andimoto/keebcu/pics/75er008.png

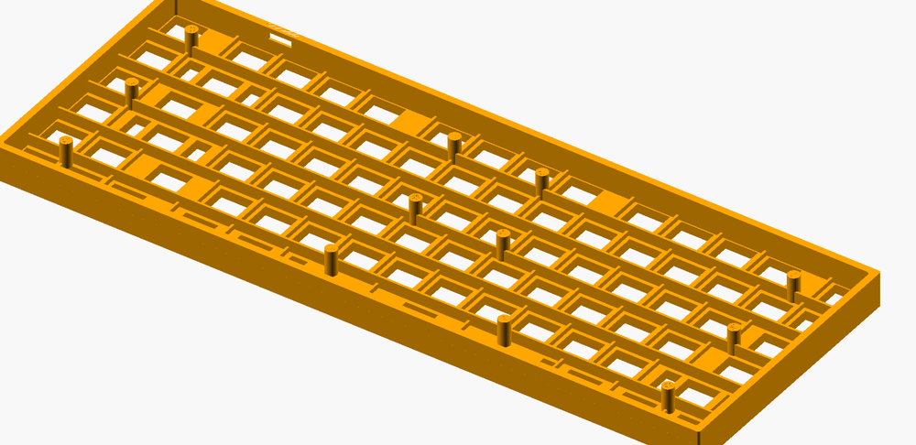
pics/75er008.png
