andimoto/keebcu/pics/75er014.png

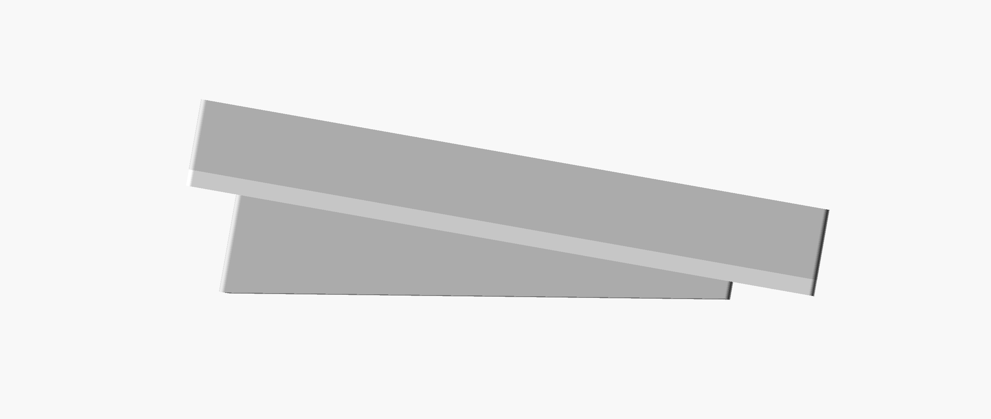
pics/75er014.png
