andimoto/keebcu/pics/75er015.png

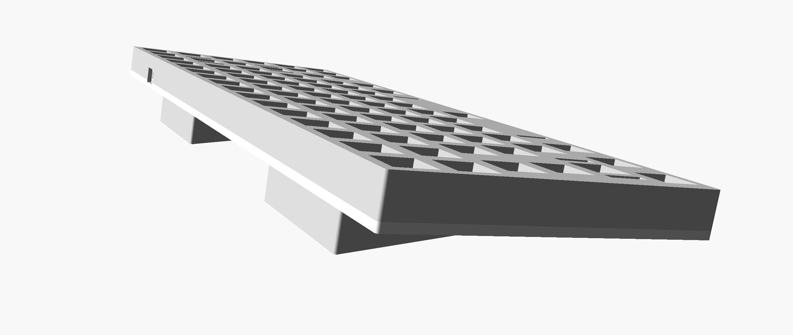
pics/75er015.png
