andimoto/keebcu/pics/75er016.png

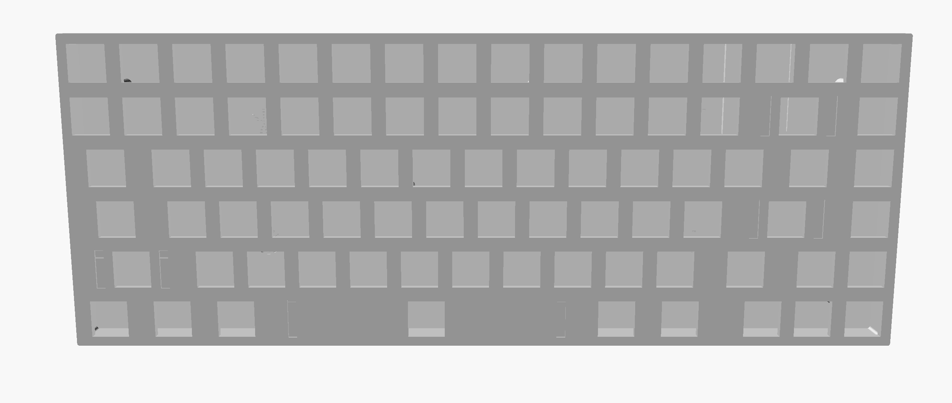
pics/75er016.png
