andimoto/keebcu/pics/75er017.png

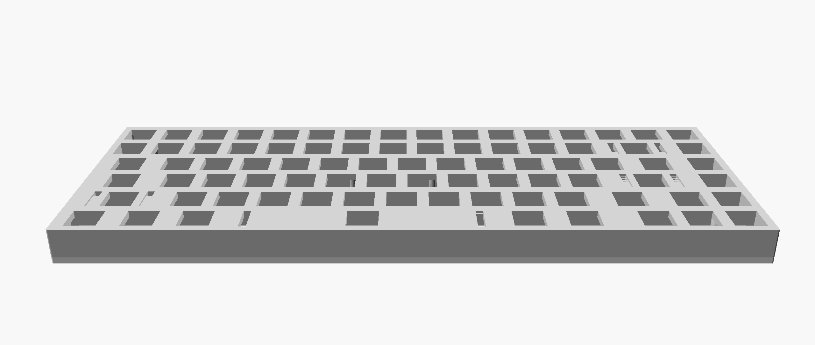
pics/75er017.png
