andimoto/keebcu/pics/andimoto7583-xda001.png

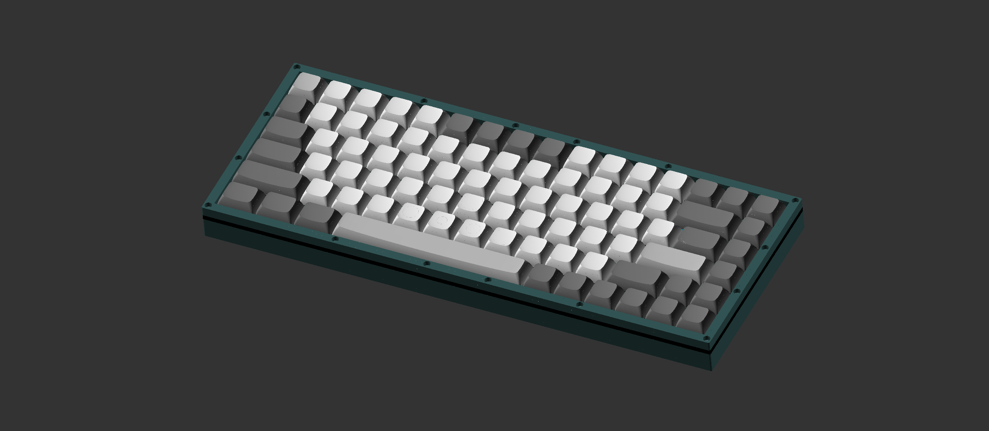
pics/andimoto7583-xda001.png
