andimoto/keebcu/pics/andimoto7583-xda002.png

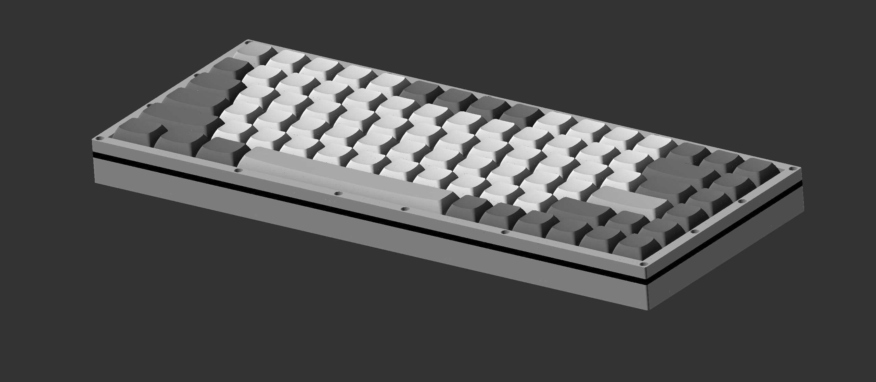
pics/andimoto7583-xda002.png
