andimoto/keebcu/pics/costar_stabs.png

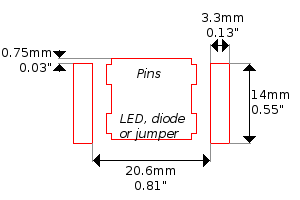
pics/costar_stabs.png
