andimoto/keebcu/pics/img/IMG_20201101_000850.jpg

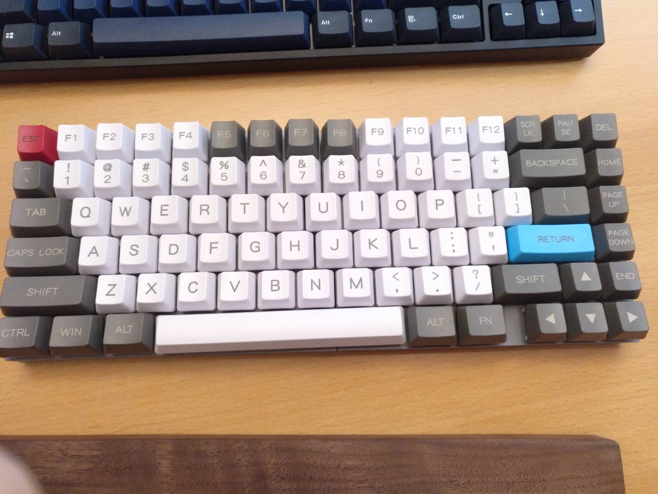
pics/img/IMG_20201101_000850.jpg
