andimoto/keebcu/pics/img/IMG_20201101_000857.jpg

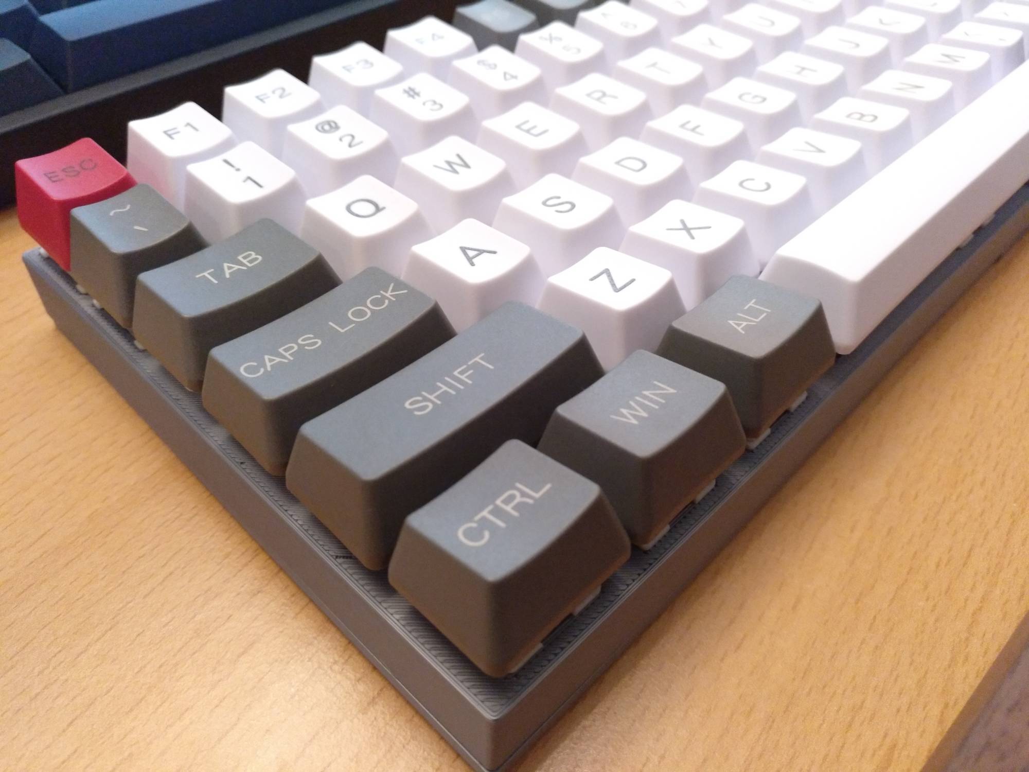
pics/img/IMG_20201101_000857.jpg
