andimoto/keebcu/pics/img/IMG_20201101_000921.jpg

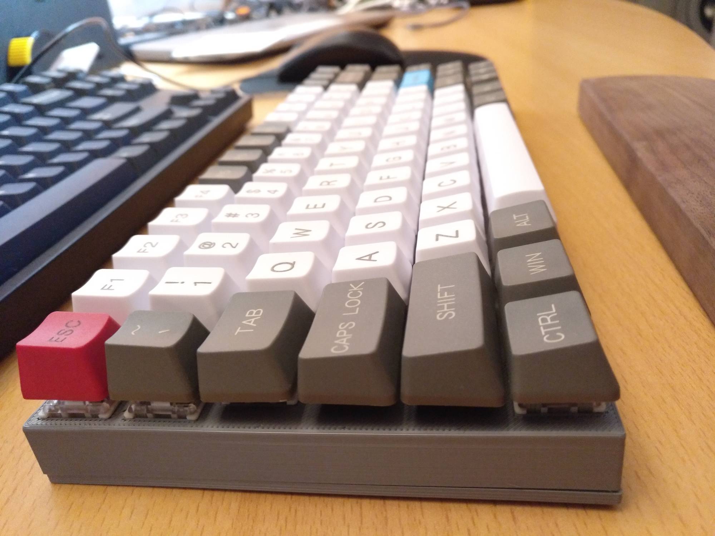
pics/img/IMG_20201101_000921.jpg
