andimoto/keebcu/pics/img/IMG_20201101_000947.jpg

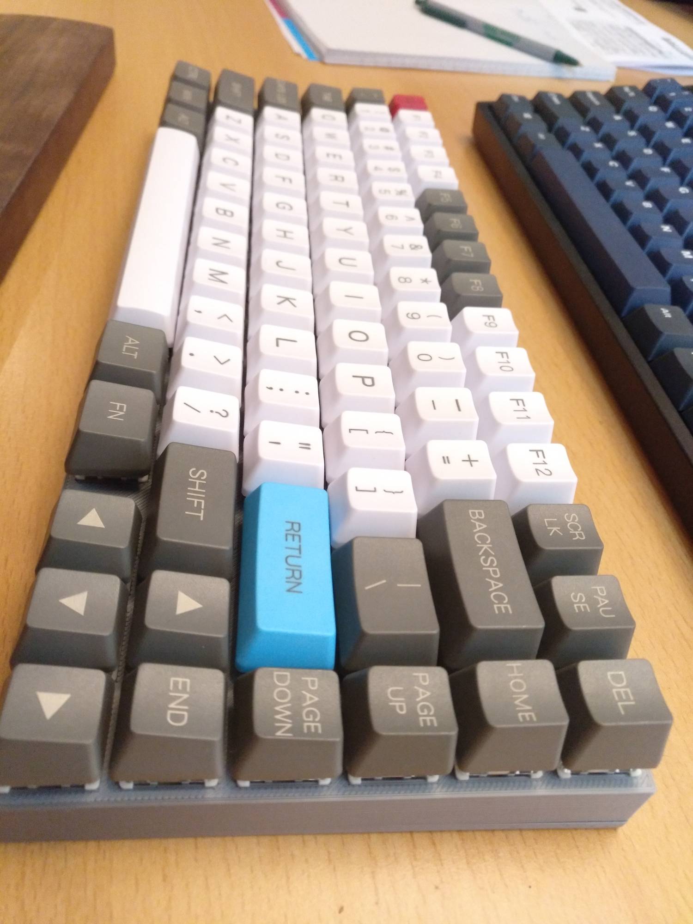
pics/img/IMG_20201101_000947.jpg
