andimoto/keebcu/pics/img/IMG_20201101_001009.jpg

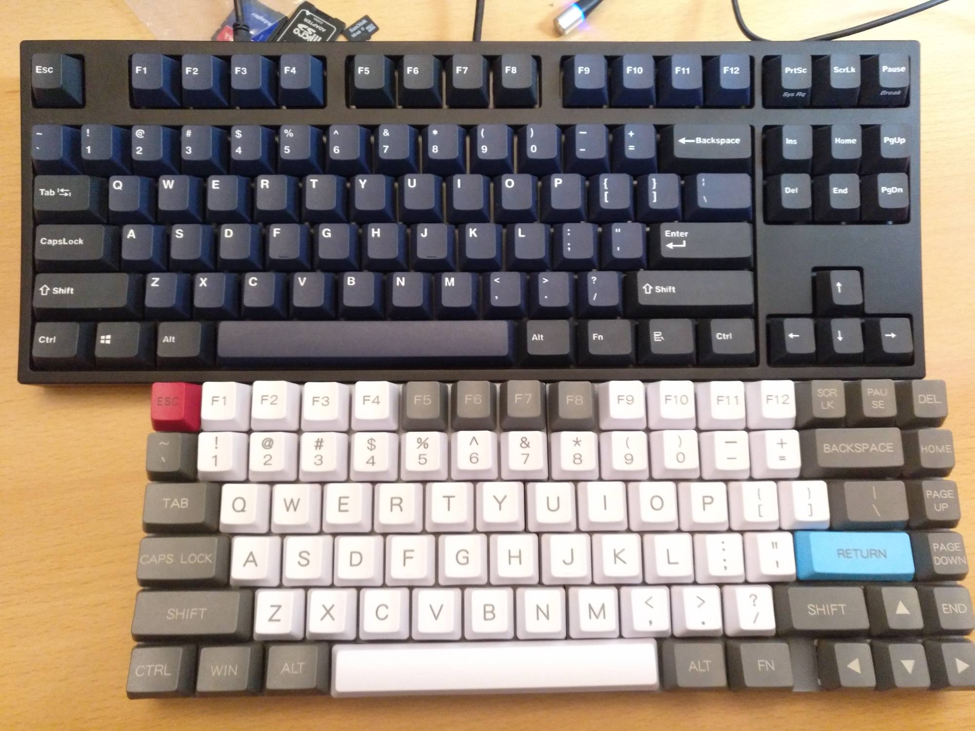
pics/img/IMG_20201101_001009.jpg
