andimoto/keebcu/pics/img/IMG_20201101_001109.jpg

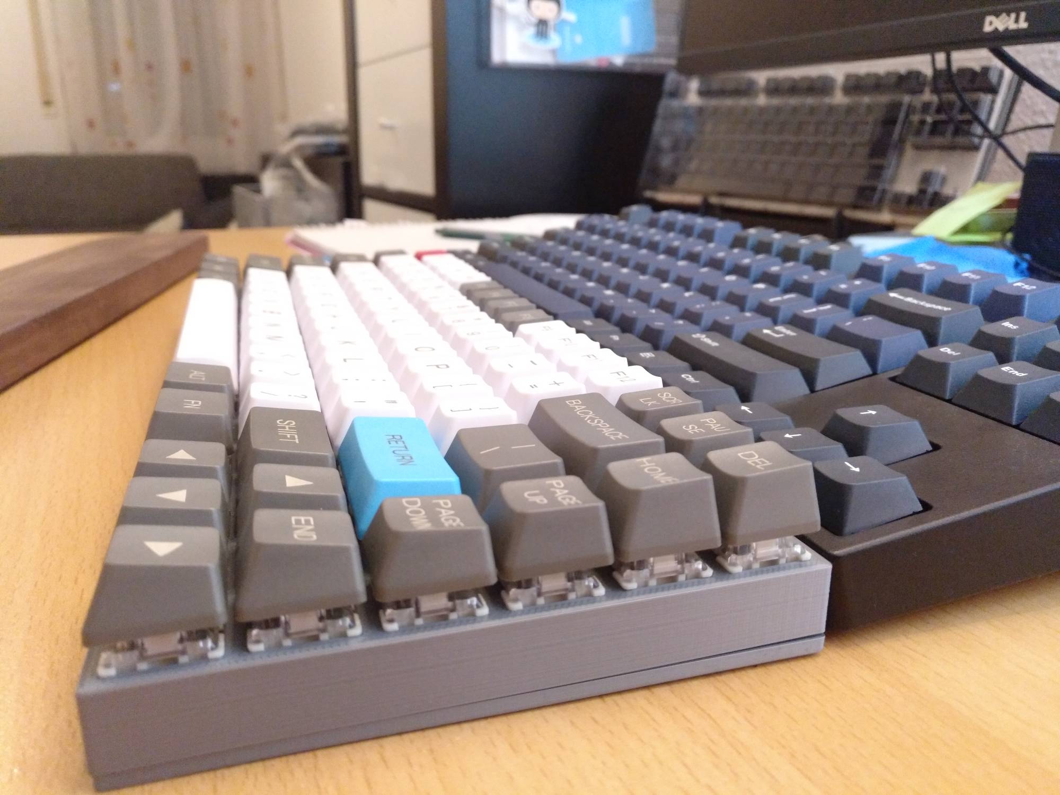
pics/img/IMG_20201101_001109.jpg
