andimoto/keebcu/pics/img/IMG_20201224_110359.jpg

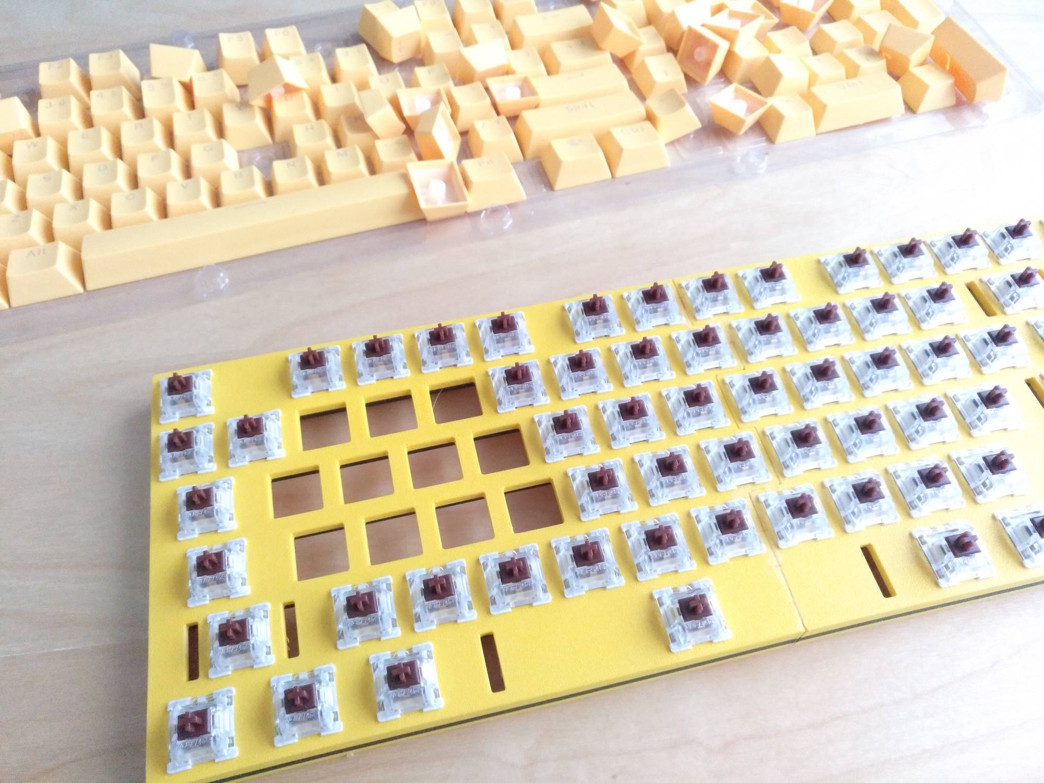
pics/img/IMG_20201224_110359.jpg
