andimoto/keebcu/pics/img/IMG_20201224_111618.jpg

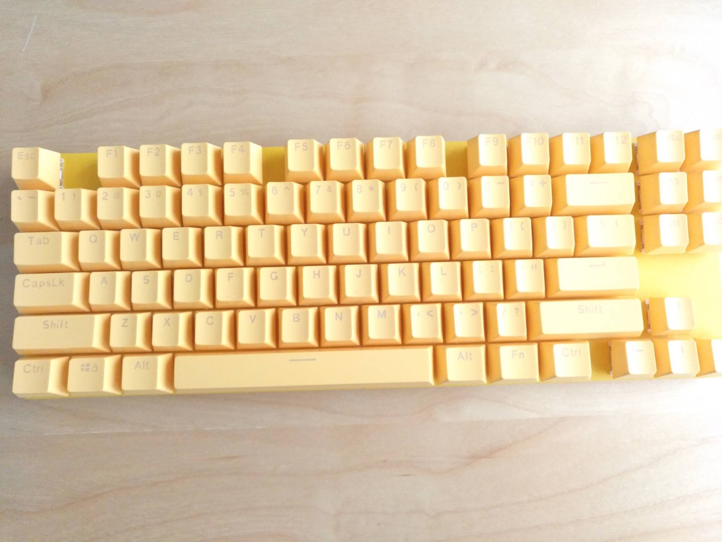
pics/img/IMG_20201224_111618.jpg
