andimoto/keebcu/pics/img/IMG_20201224_111624.jpg

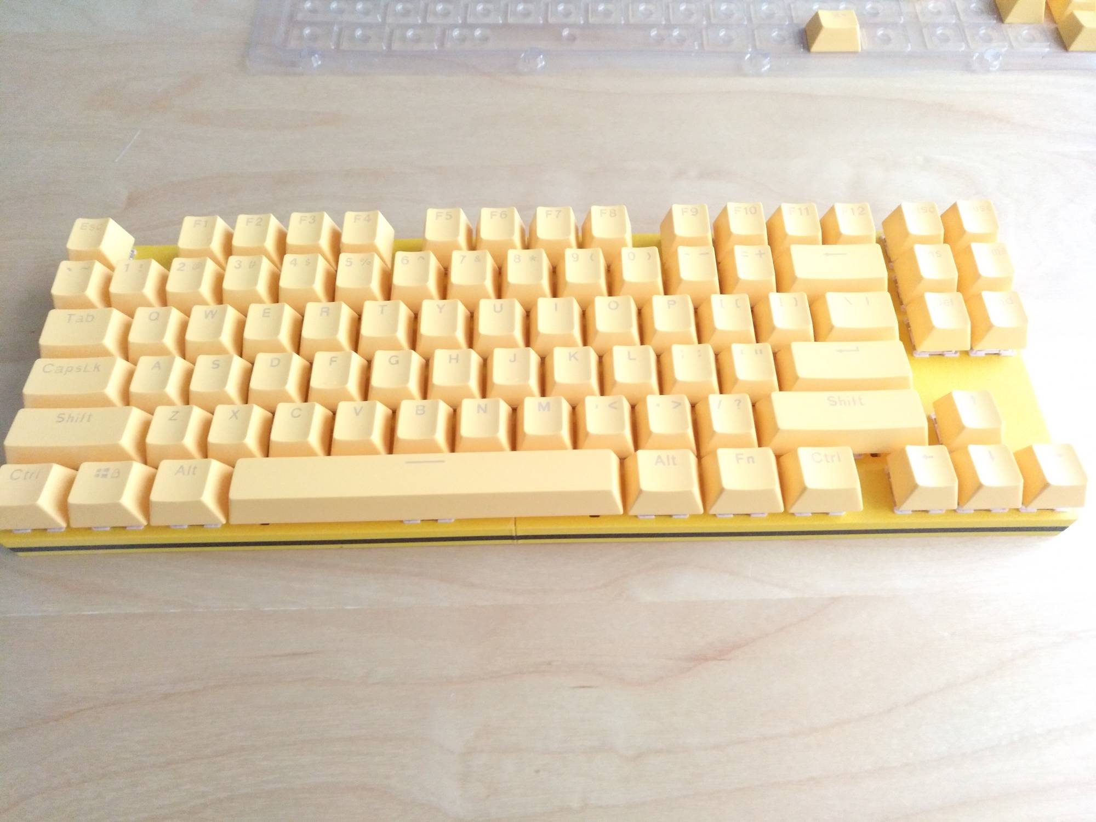
pics/img/IMG_20201224_111624.jpg
