andimoto/keebcu/pics/img/IMG_20201224_111630.jpg

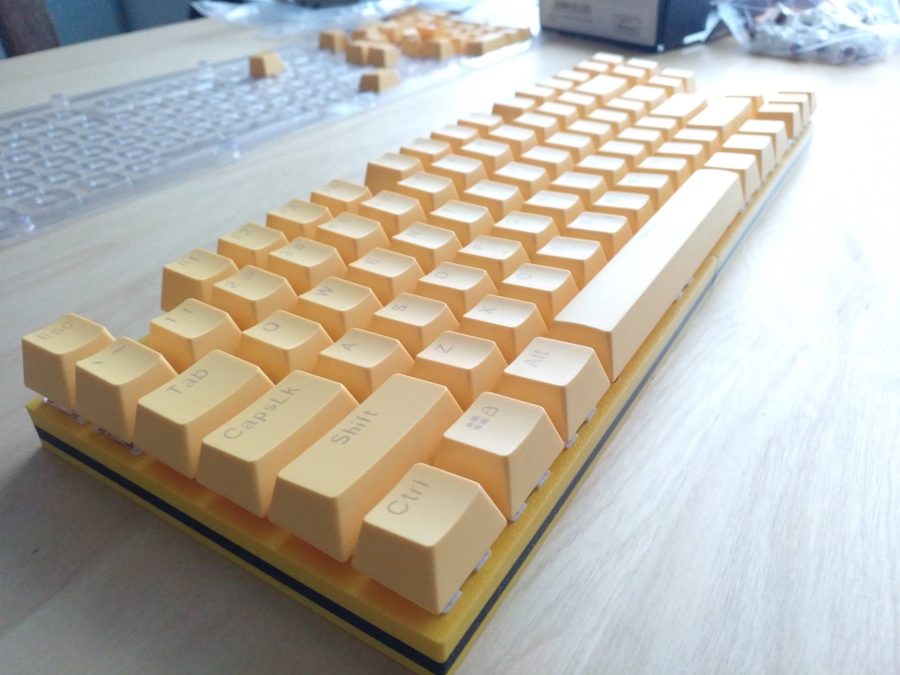
pics/img/IMG_20201224_111630.jpg
