andimoto/keebcu/pics/img/IMG_20201224_111640.jpg

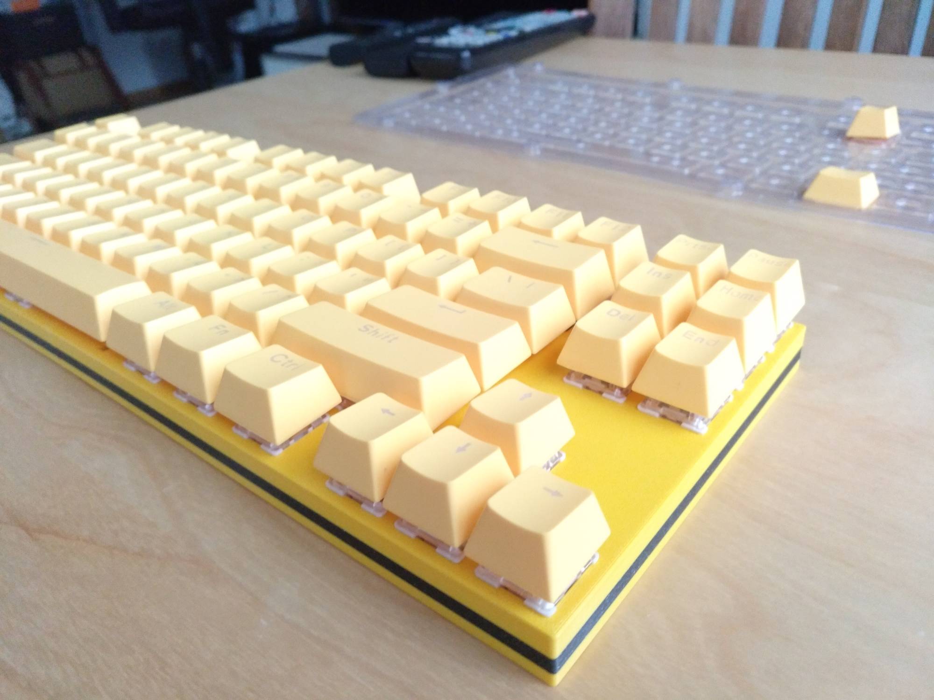
pics/img/IMG_20201224_111640.jpg
