andimoto/keebcu/pics/img/IMG_20201224_111739.jpg

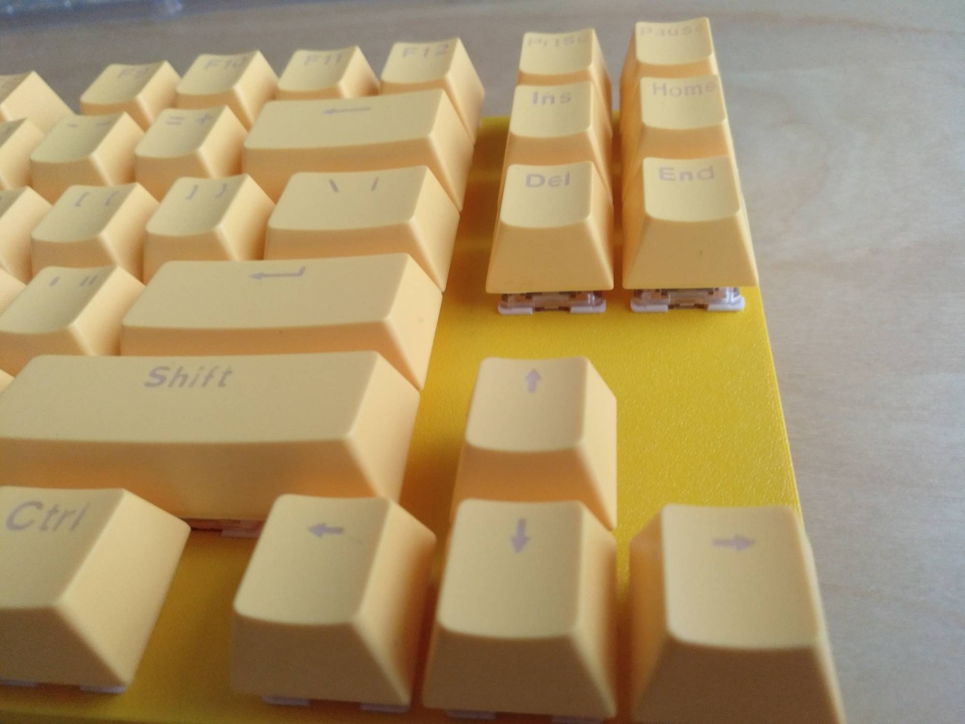
pics/img/IMG_20201224_111739.jpg
