andimoto/keebcu/pics/img/IMG_20201224_111744.jpg

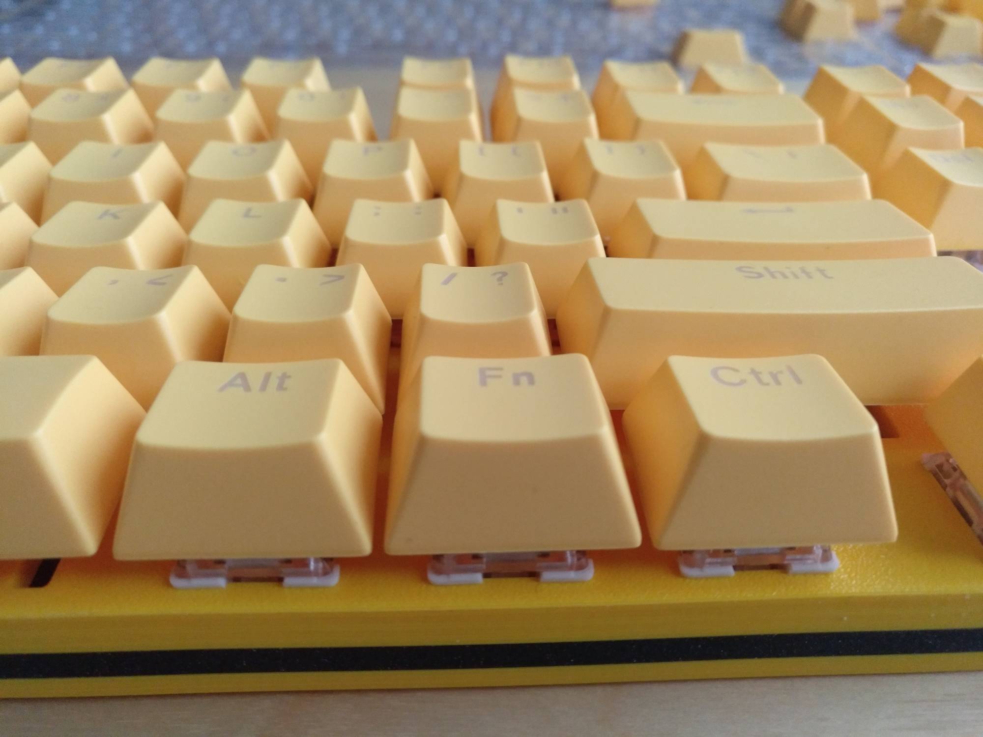
pics/img/IMG_20201224_111744.jpg
