andimoto/keebcu/pics/img/IMG_20201224_111752.jpg

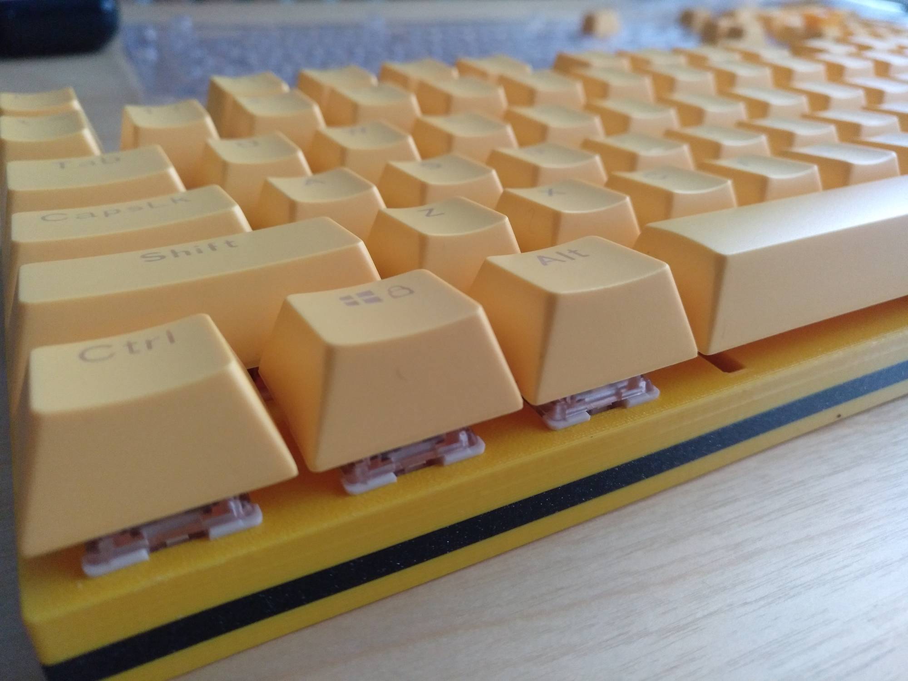
pics/img/IMG_20201224_111752.jpg
