andimoto/keebcu/pics/img/IMG_20201228_204647.jpg

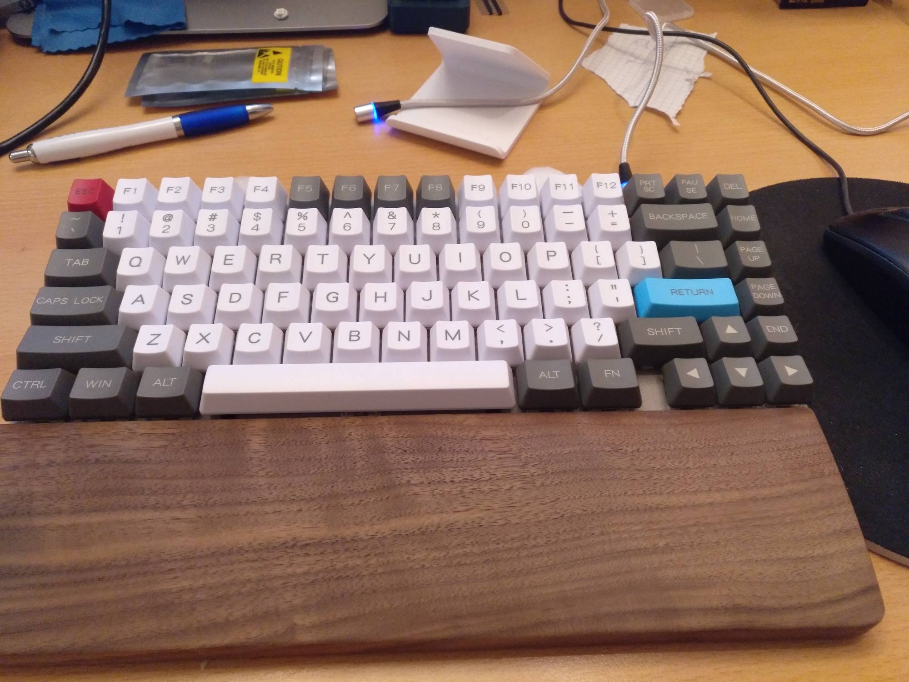
pics/img/IMG_20201228_204647.jpg
