andimoto/keebcu/pics/img/IMG_20210111_151033.jpg

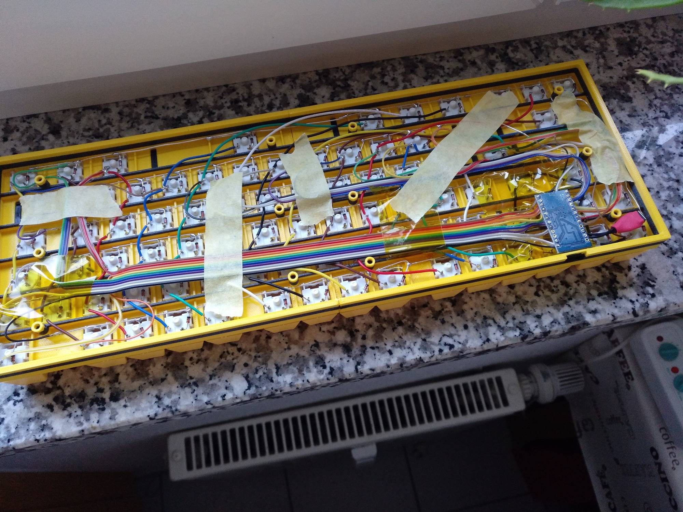
pics/img/IMG_20210111_151033.jpg
