andimoto/keebcu/pics/img/IMG_20210111_151047.jpg

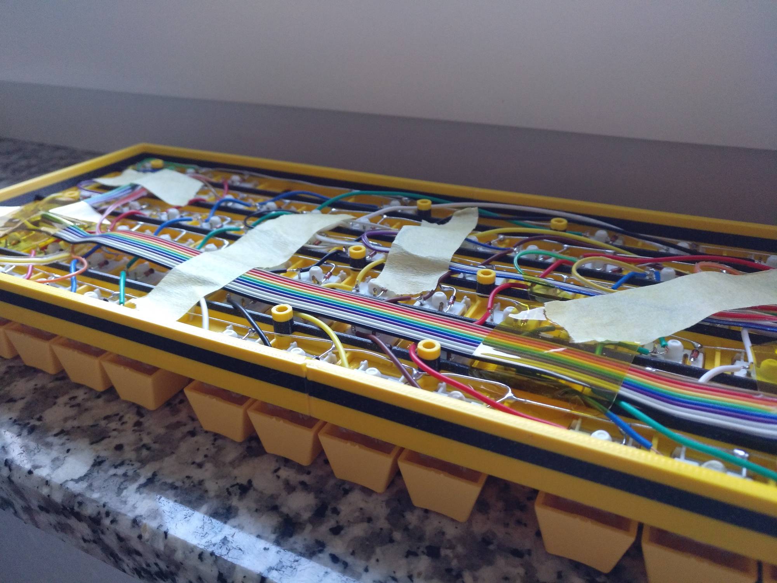
pics/img/IMG_20210111_151047.jpg
