andimoto/keebcu/pics/img/IMG_20210111_151052.jpg

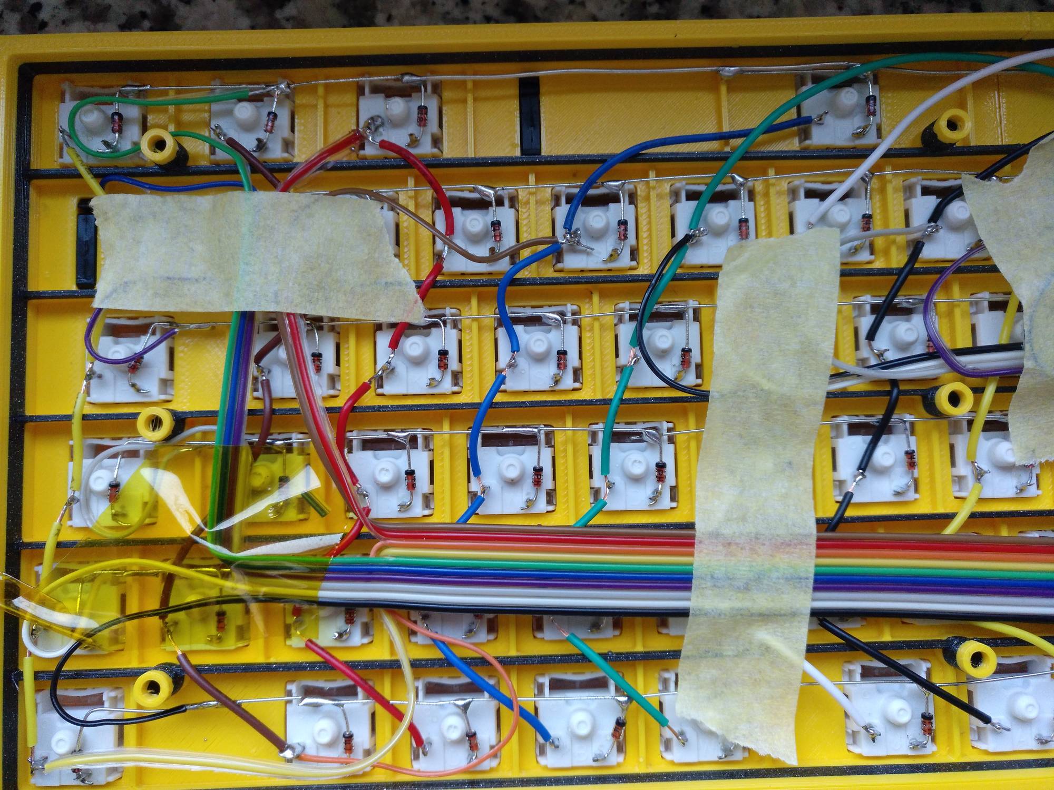
pics/img/IMG_20210111_151052.jpg
