andimoto/keebcu/pics/img/IMG_20210111_151100.jpg

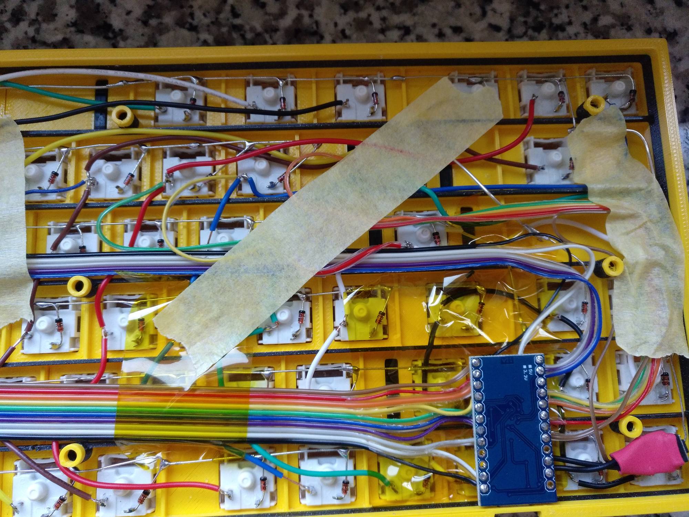
pics/img/IMG_20210111_151100.jpg
