andimoto/keebcu/pics/img/IMG_20210111_151114.jpg

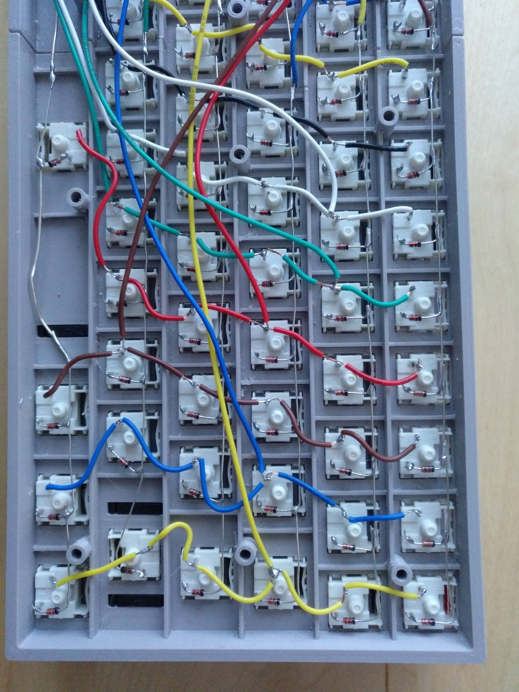
pics/img/IMG_20210111_151114.jpg
