andimoto/keebcu/pics/img/IMG_20210111_151118.jpg

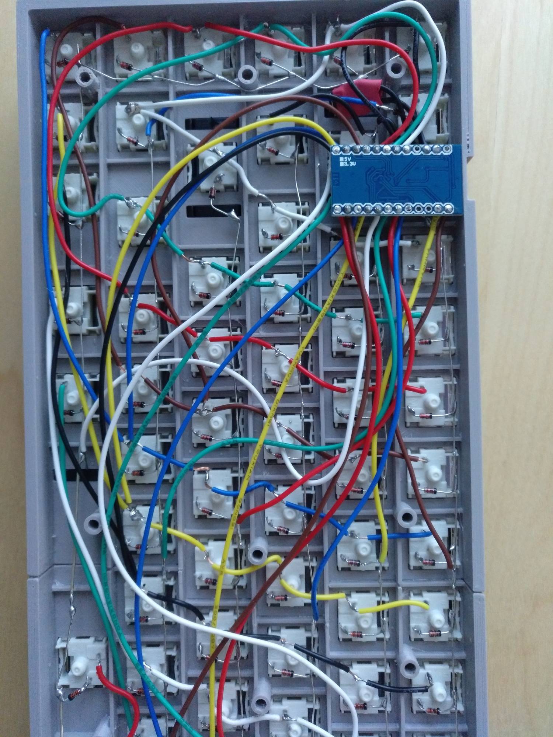
pics/img/IMG_20210111_151118.jpg
