andimoto/keebcu/pics/img/IMG_20210119_213742.jpg

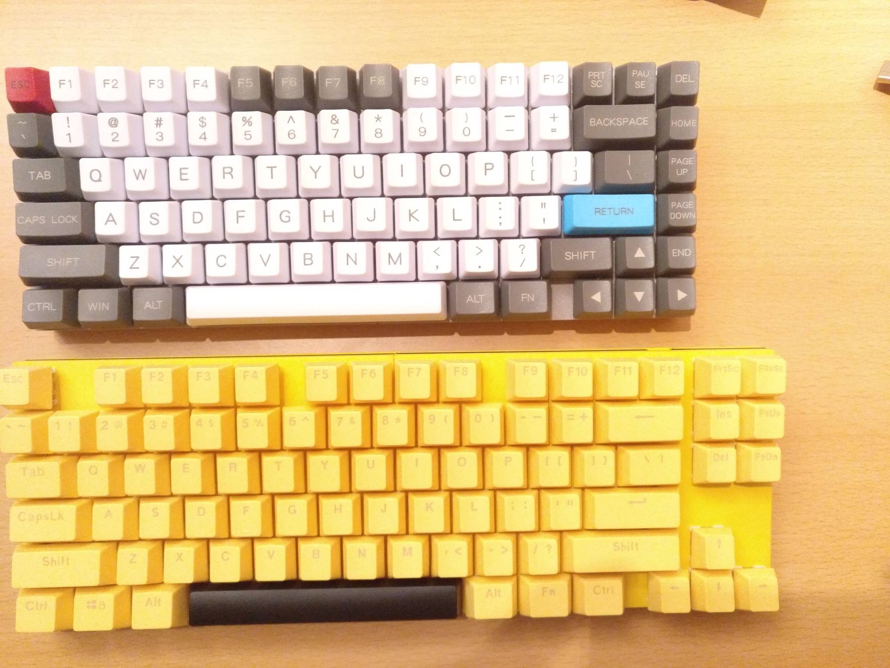
pics/img/IMG_20210119_213742.jpg
