andimoto/keebcu/pics/img/IMG_20210318_140613.jpg

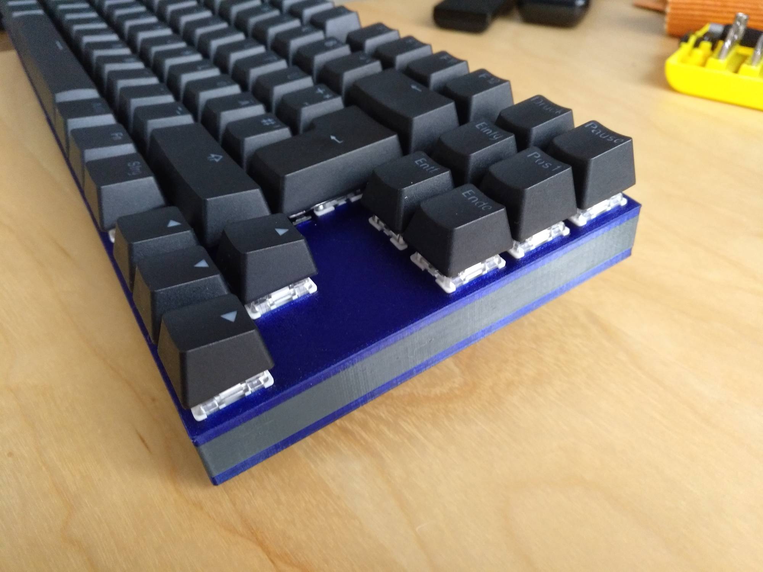
pics/img/IMG_20210318_140613.jpg
