andimoto/keebcu/pics/img/IMG_20210318_140618.jpg

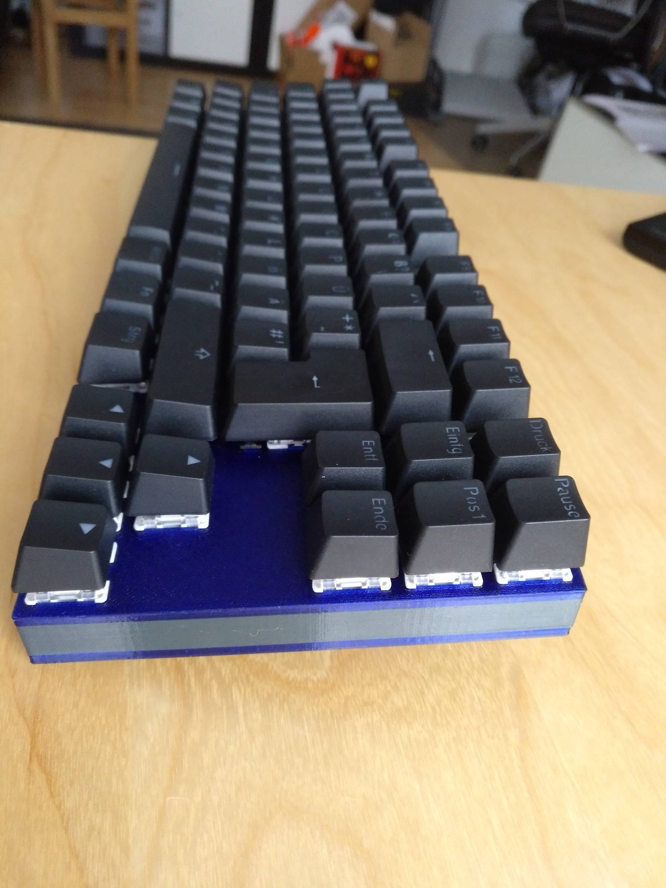
pics/img/IMG_20210318_140618.jpg
