andimoto/keebcu/pics/img/IMG_20210318_140654.jpg

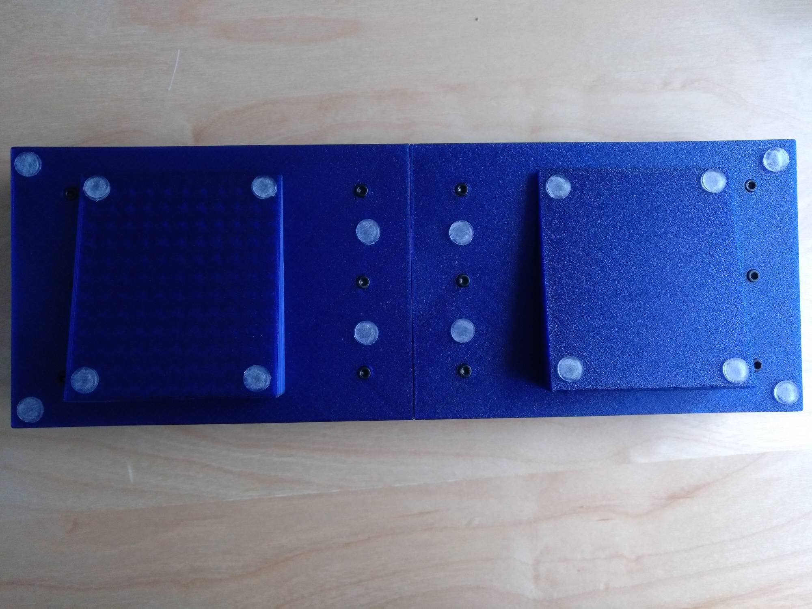
pics/img/IMG_20210318_140654.jpg
