andimoto/keebcu/pics/img/IMG_20210318_175820.jpg

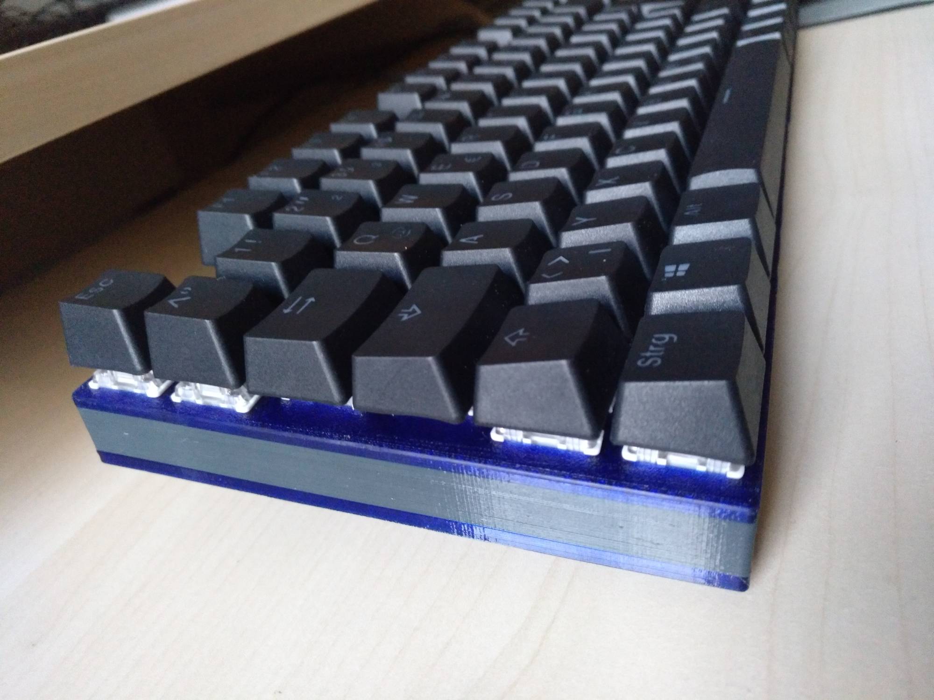
pics/img/IMG_20210318_175820.jpg
