andimoto/keebcu/pics/img/IMG_20210318_175835.jpg

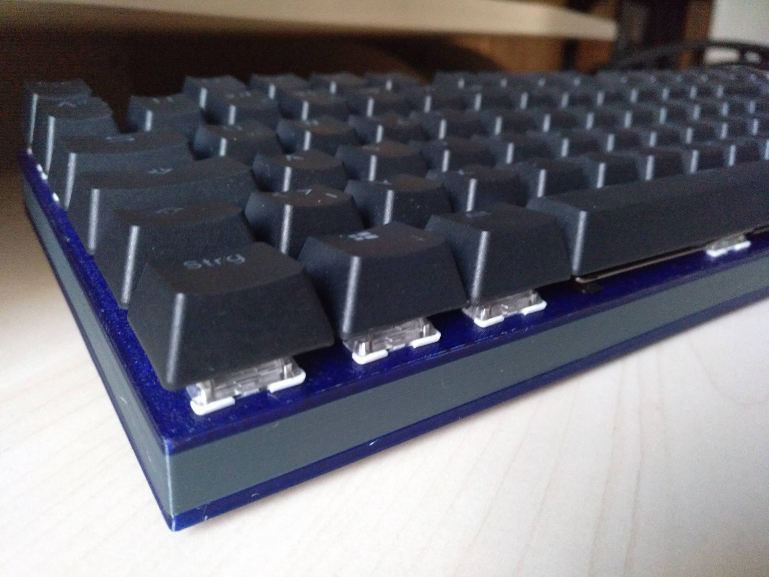
pics/img/IMG_20210318_175835.jpg
