andimoto/keebcu/pics/img/IMG_20210405_204525.jpg

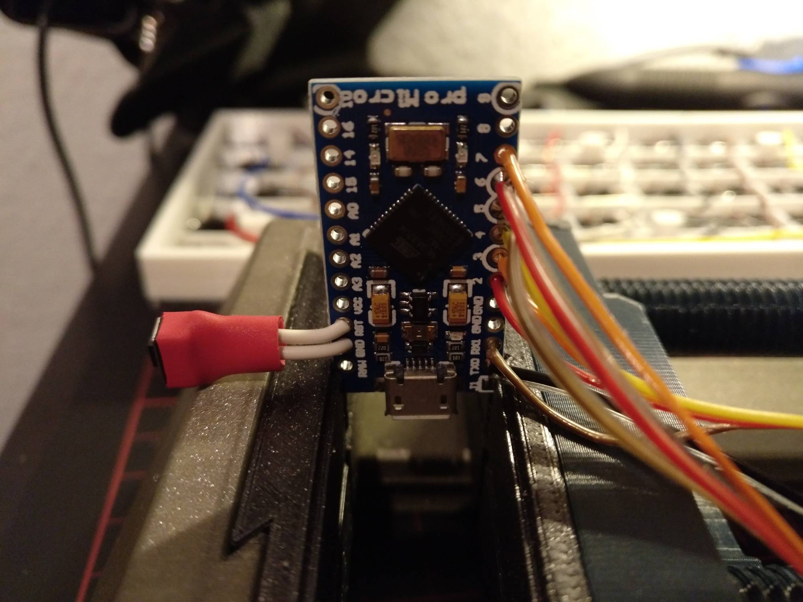
pics/img/IMG_20210405_204525.jpg
