andimoto/keebcu/pics/img/IMG_20210406_151226.jpg

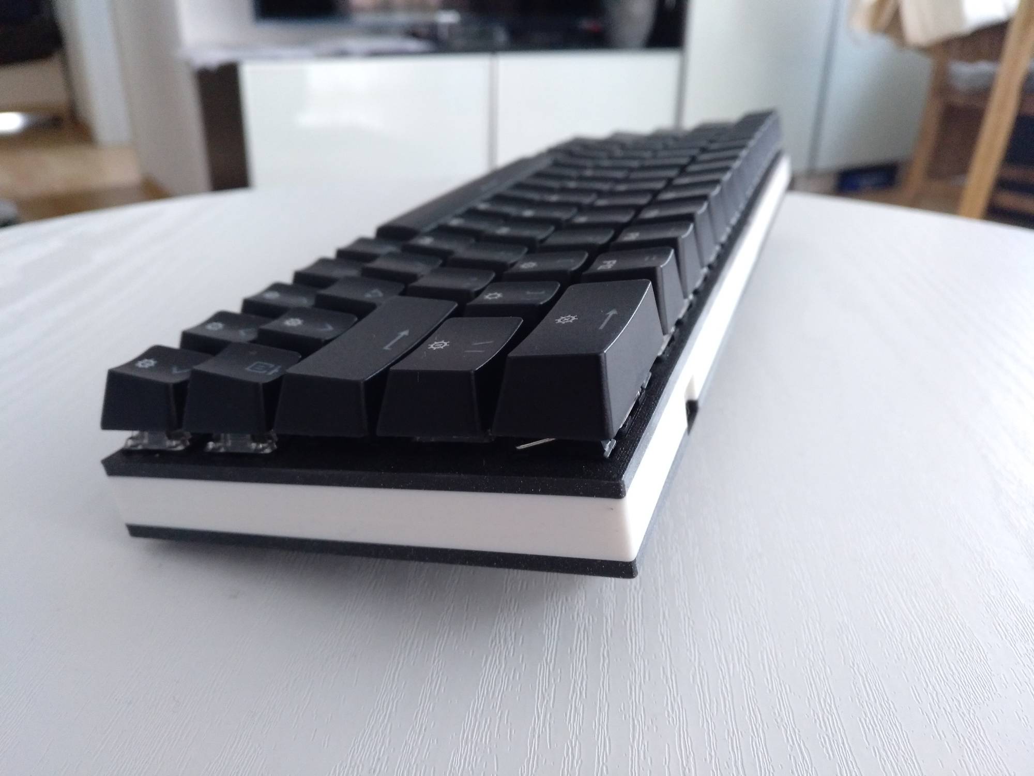
pics/img/IMG_20210406_151226.jpg
