andimoto/keebcu/pics/img/IMG_20210406_151432.jpg

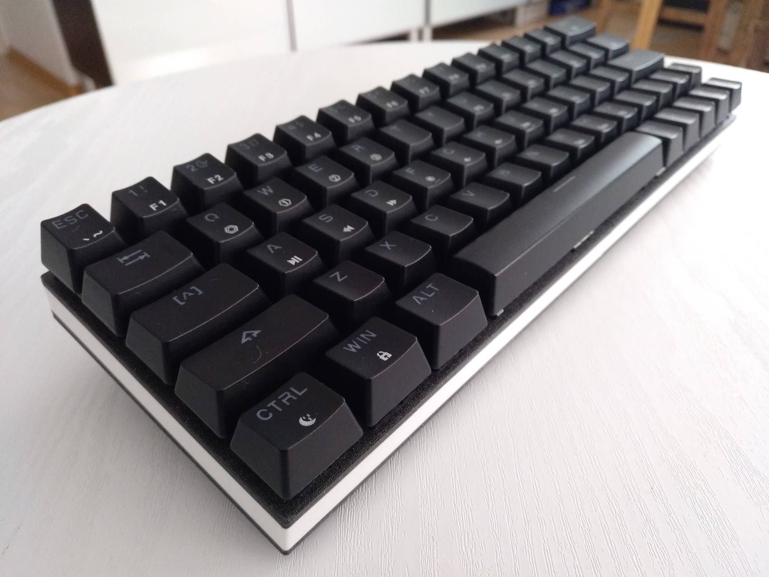
pics/img/IMG_20210406_151432.jpg
