andimoto/keebcu/pics/img/IMG_20210406_151457.jpg

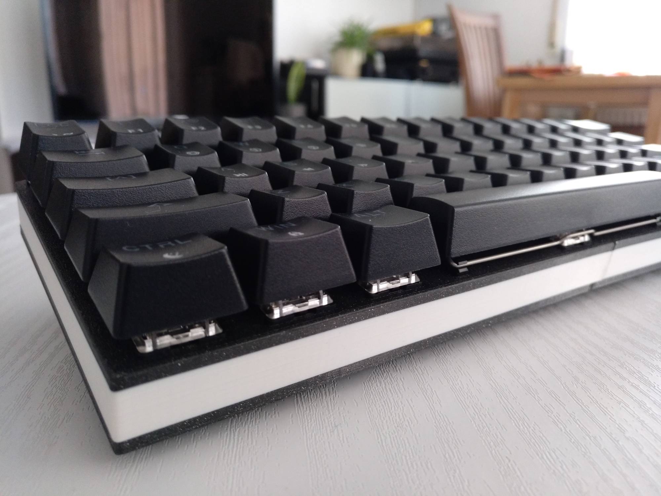
pics/img/IMG_20210406_151457.jpg
