andimoto/keebcu/pics/img/screwHolesColorChange.jpg

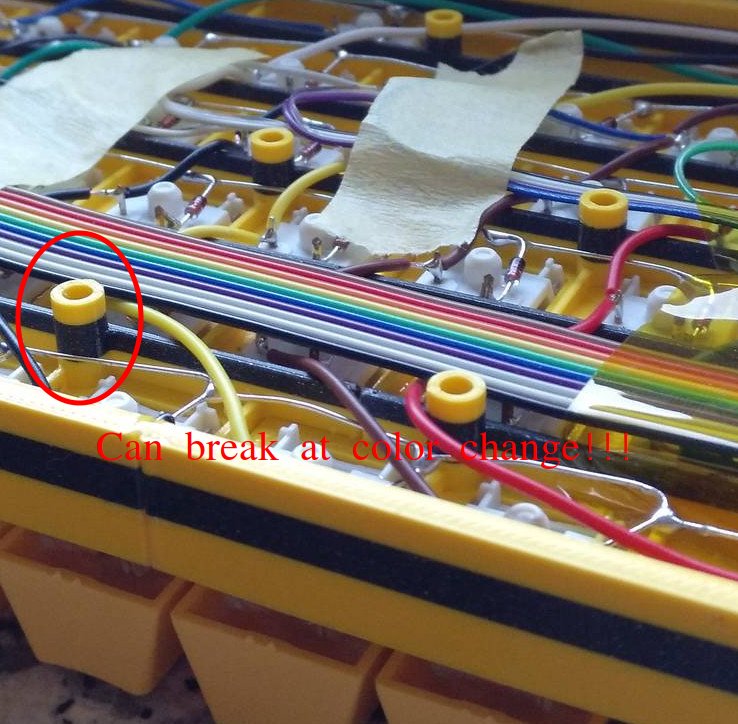
pics/img/screwHolesColorChange.jpg
