andimoto/keebcu/pics/pics/andimoto75Q1iso-001.jpg

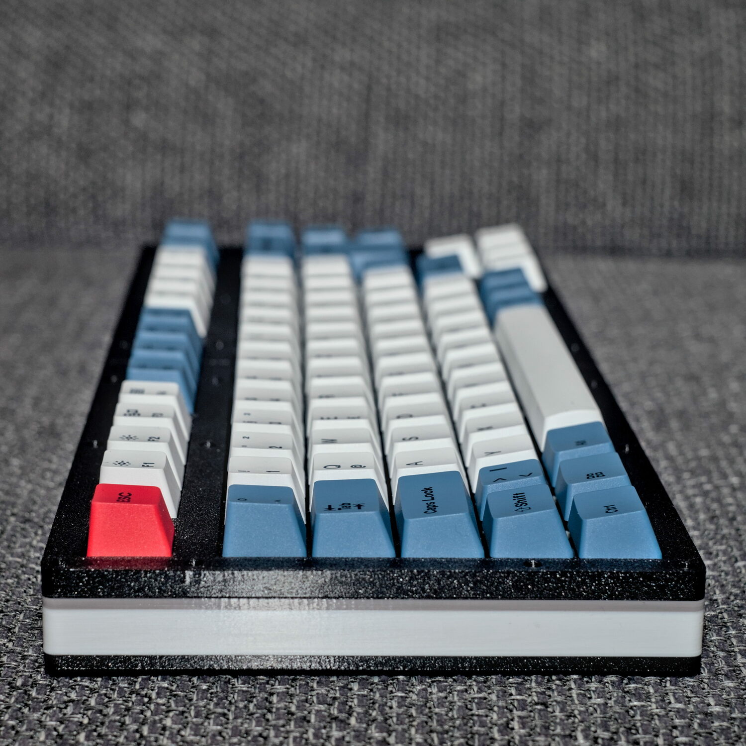
pics/pics/andimoto75Q1iso-001.jpg
