andimoto/keebcu/pics/pics/andimoto75Q1iso-003.jpg

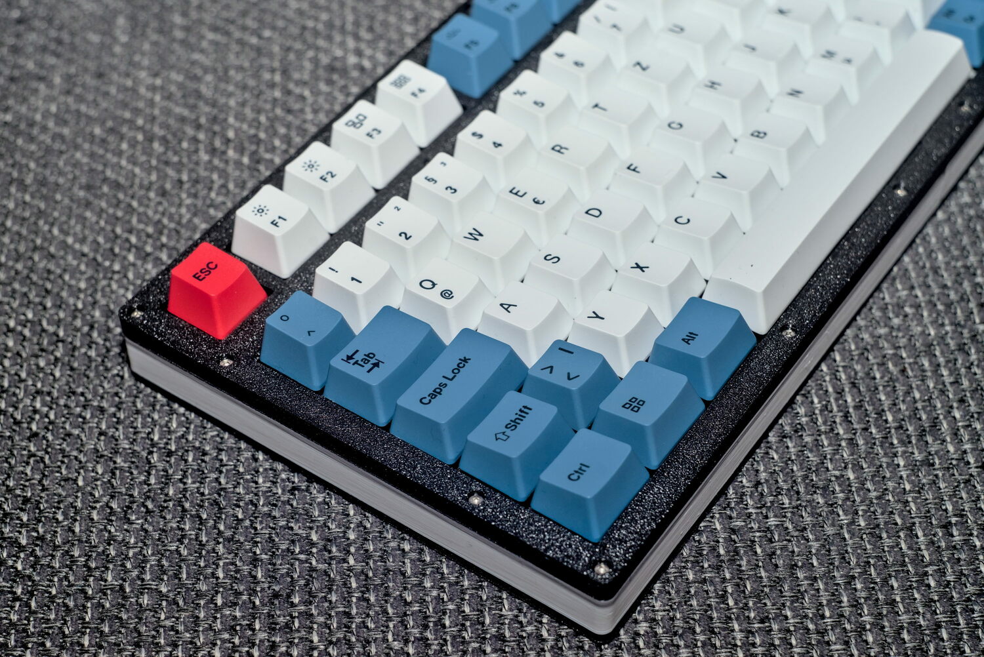
pics/pics/andimoto75Q1iso-003.jpg
