andimoto/keebcu/pics/pics/andimoto75Q1iso-005.jpg

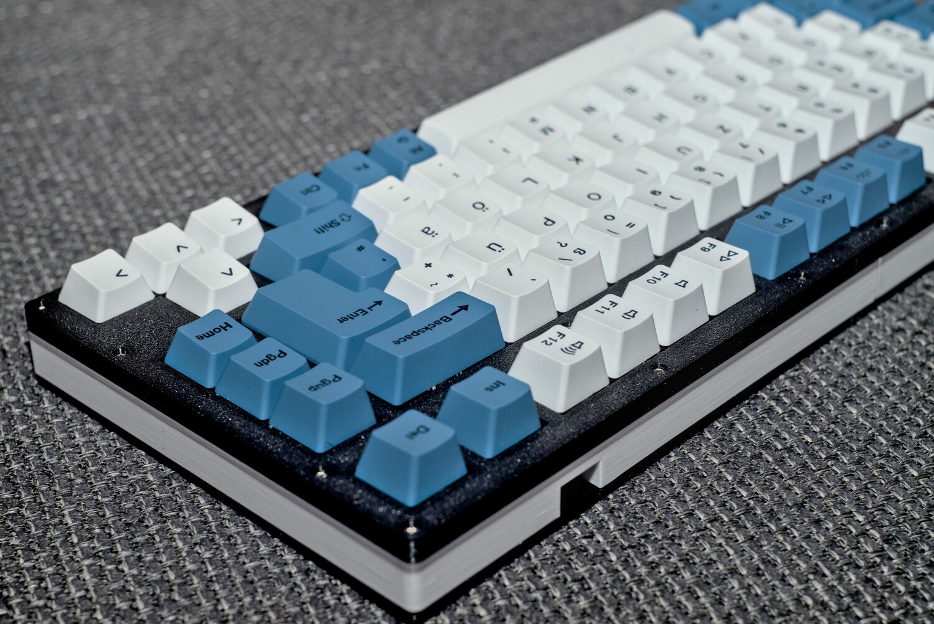
pics/pics/andimoto75Q1iso-005.jpg
