andimoto/keebcu/pics/pics/andimoto75Q1iso-008.jpg

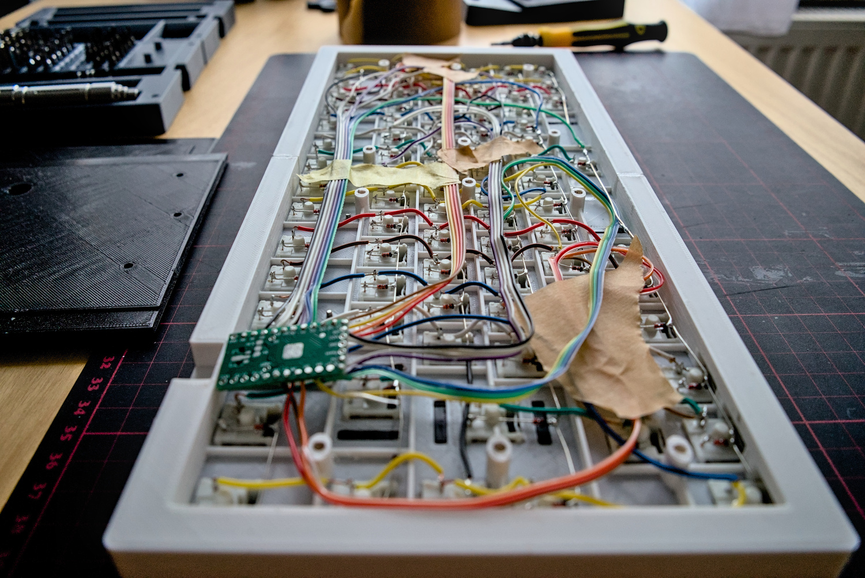
pics/pics/andimoto75Q1iso-008.jpg
