andimoto/keebcu/pics/pics/andimoto75Q1iso-009.jpg

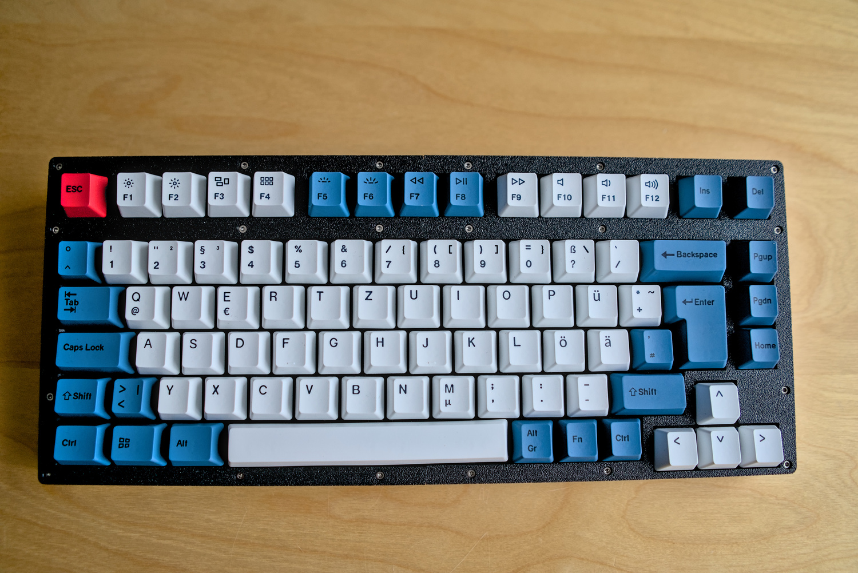
pics/pics/andimoto75Q1iso-009.jpg
