andimoto/keebcu/pics/pics/andimoto75Q1iso-010.jpg

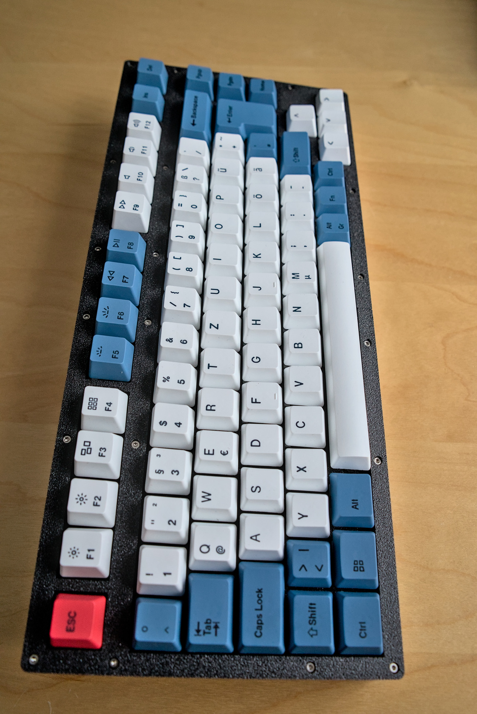
pics/pics/andimoto75Q1iso-010.jpg
