andimoto/keebcu/pics/pics/andimoto75Q1iso-011.jpg

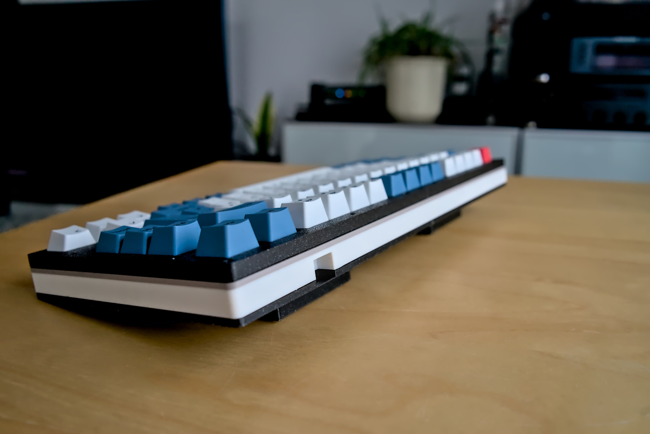
pics/pics/andimoto75Q1iso-011.jpg
