andimoto/keebcu/pics/pics/andimoto75Q1iso-012.jpg

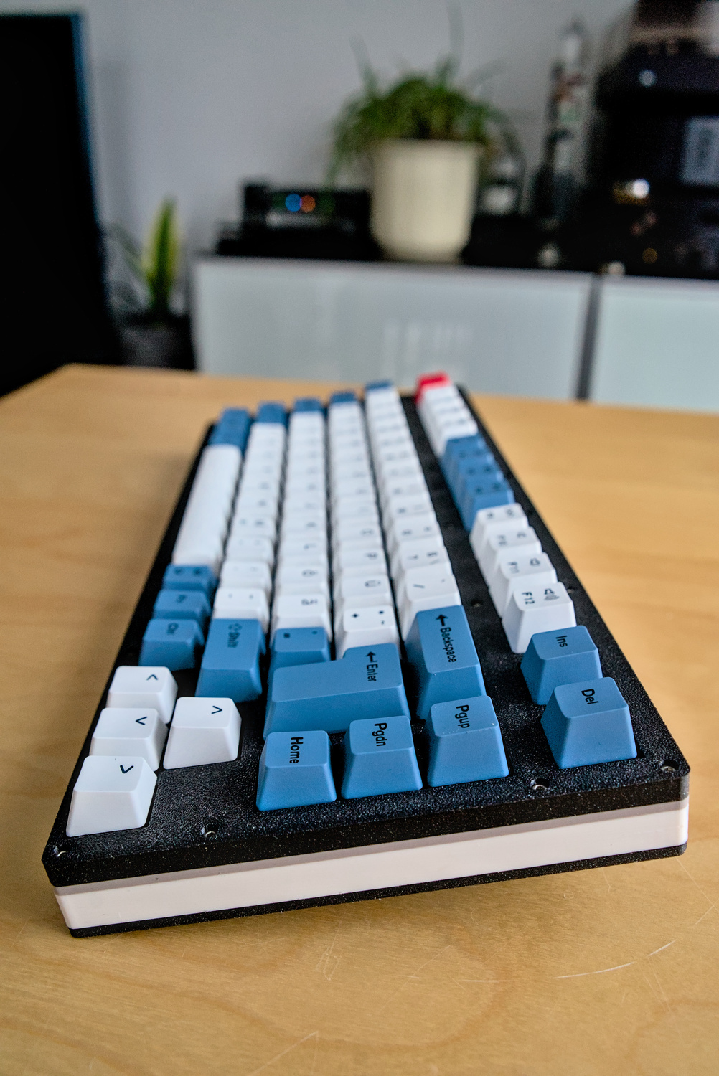
pics/pics/andimoto75Q1iso-012.jpg
