andimoto/keebcu/pics/pics/keebcu_002.JPG

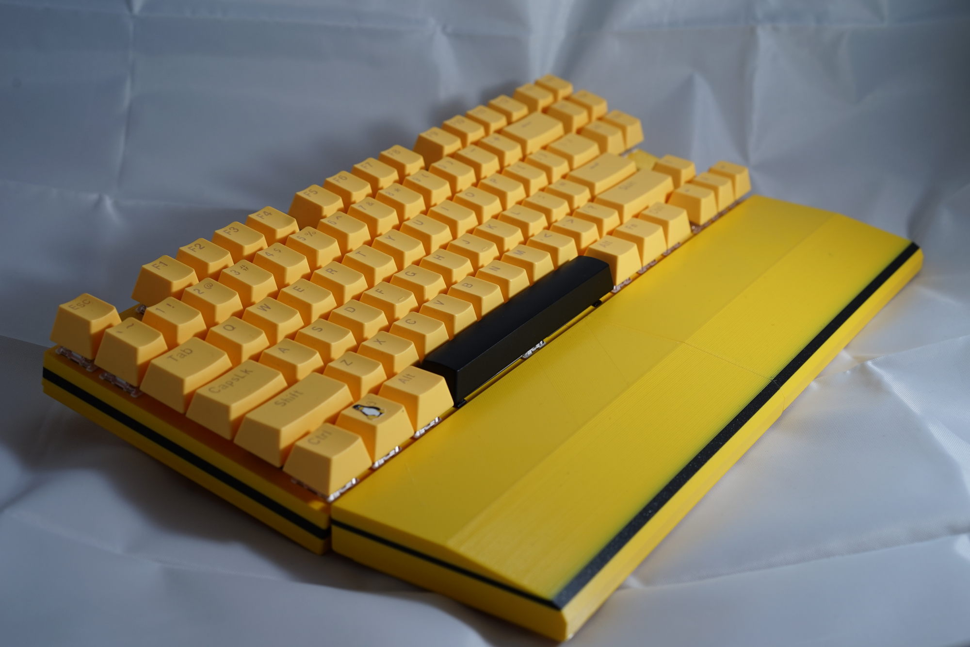
pics/pics/keebcu_002.JPG
