andimoto/keebcu/pics/pics/keebcu_006.JPG

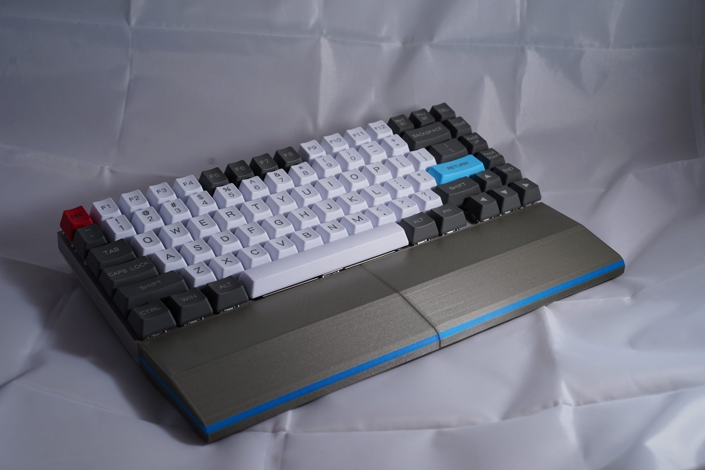
pics/pics/keebcu_006.JPG
