andimoto/keebcu/pics/pics/keebcu_007.JPG

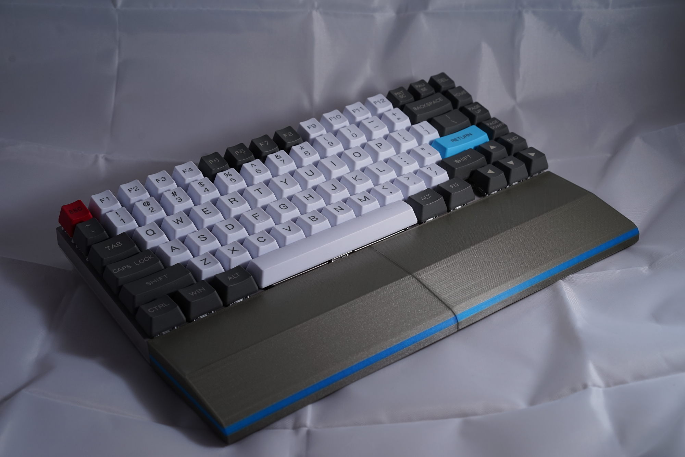
pics/pics/keebcu_007.JPG
