andimoto/keebcu/pics/pics/keebcu_008.JPG

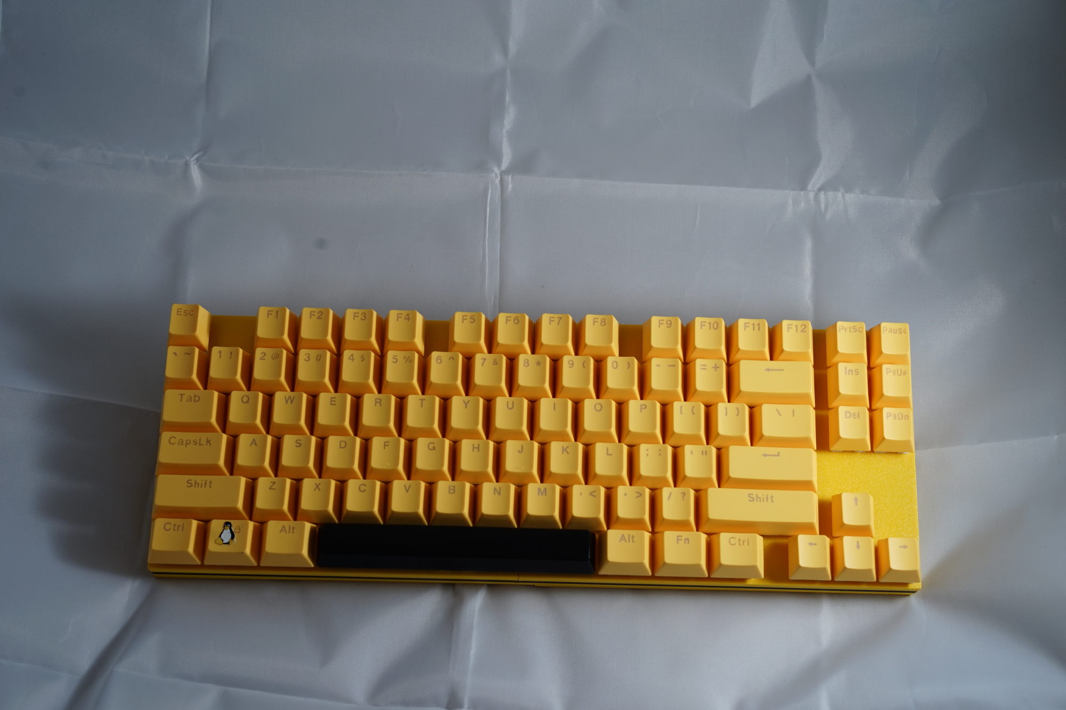
pics/pics/keebcu_008.JPG
