andimoto/keebcu/pics/pics/keebcu_010.JPG

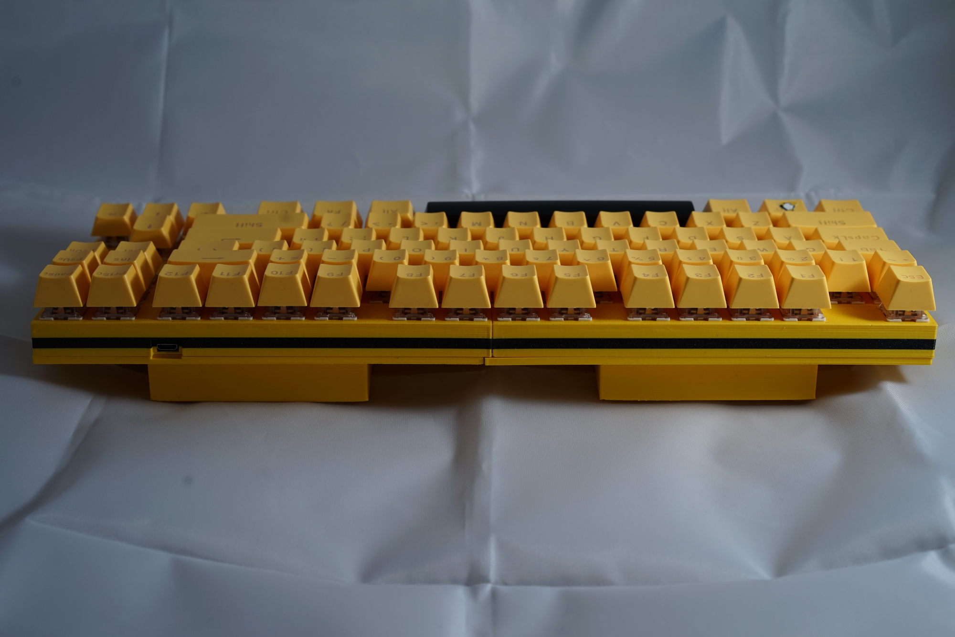
pics/pics/keebcu_010.JPG
