andimoto/keebcu/pics/pics/keebcu_011.JPG

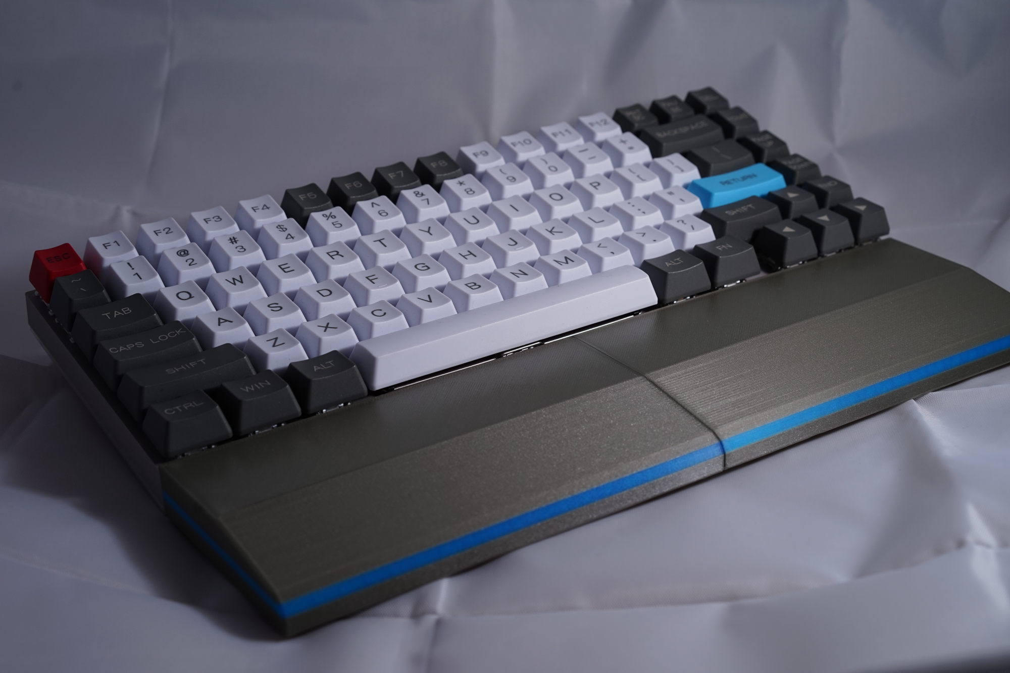
pics/pics/keebcu_011.JPG
