andimoto/keebcu/pics/pics/keebcu_012.JPG

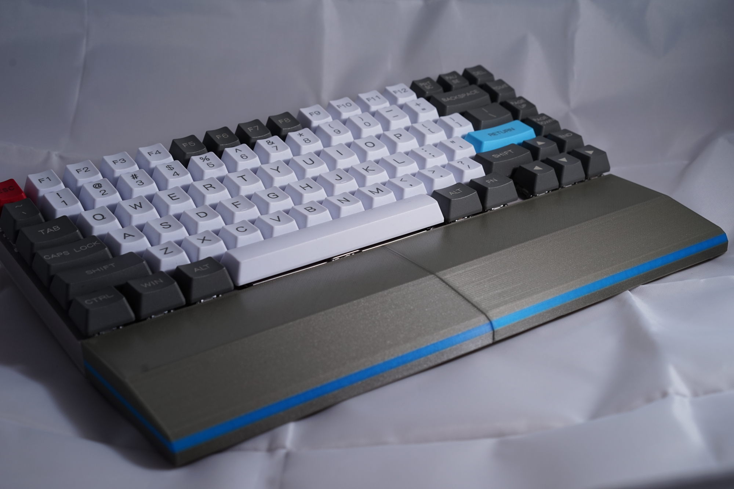
pics/pics/keebcu_012.JPG
