andimoto/keebcu/pics/pics/macro002.JPG

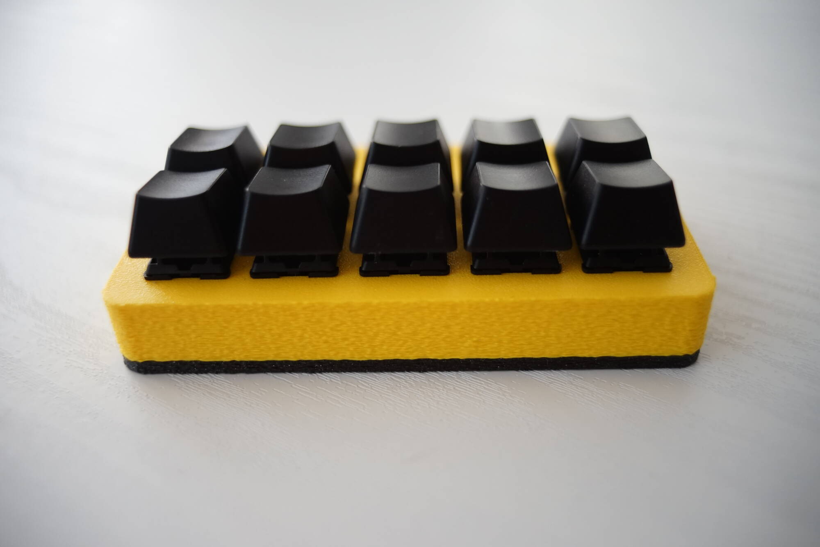
pics/pics/macro002.JPG
