andimoto/keebcu/pics/pics/numpad_001.jpg

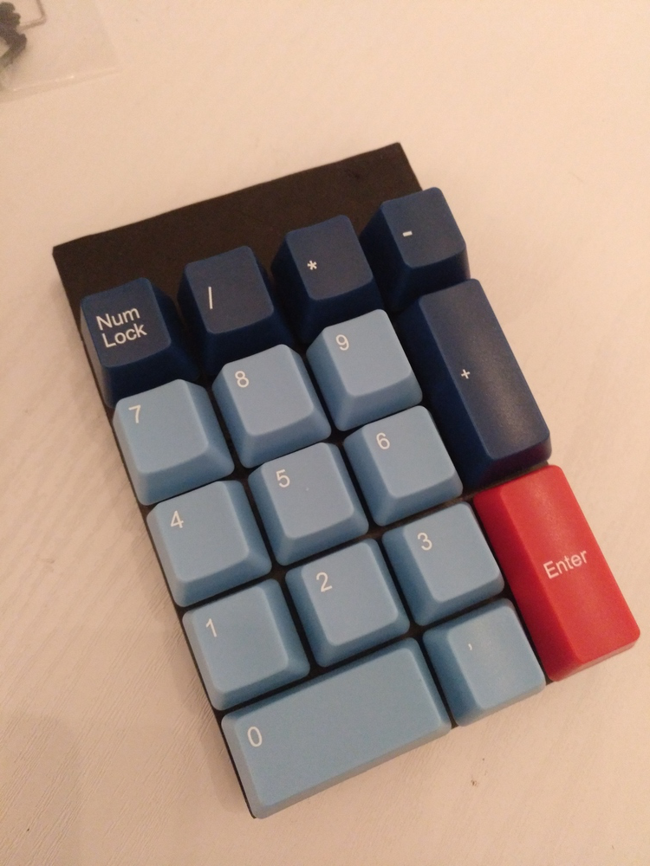
pics/pics/numpad_001.jpg
