andimoto/keebcu/pics/usbCutoutPlaceing.png

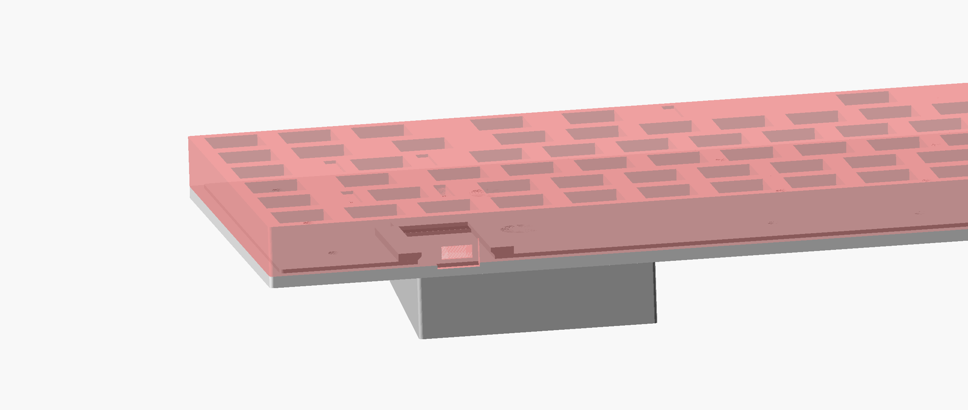
pics/usbCutoutPlaceing.png
