andimoto/keebcu/pics/wrist36L.png

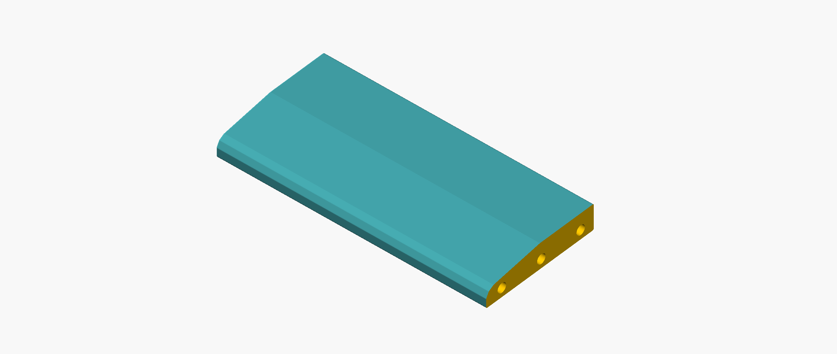
pics/wrist36L.png
