andimoto/keebcu/pics/wrist36R.png

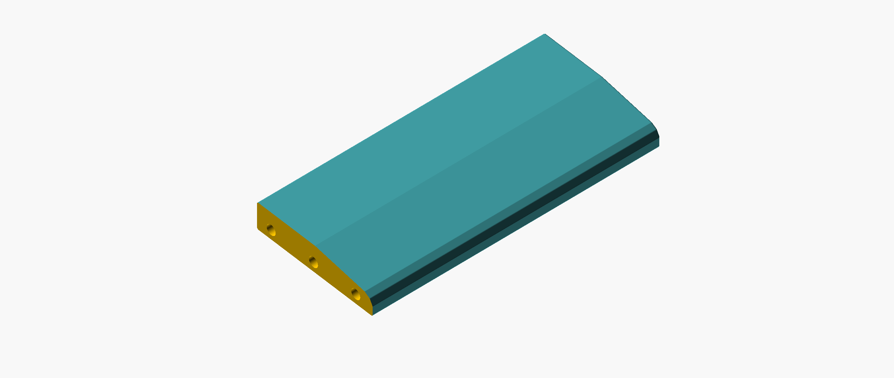
pics/wrist36R.png
