andimoto/keebcu/pics/wristComplete.png

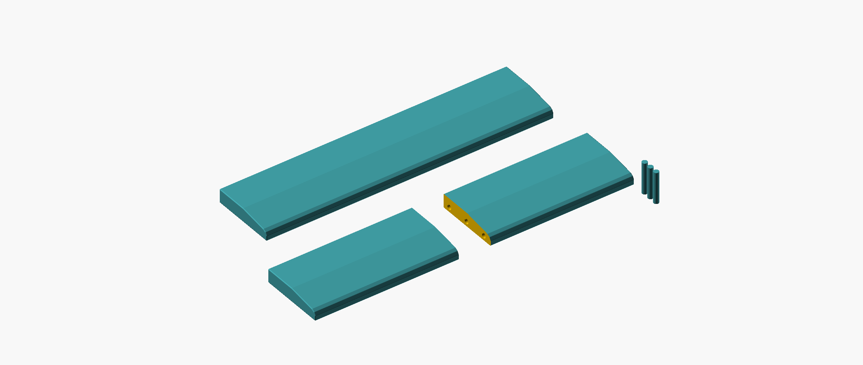
pics/wristComplete.png
