andimoto/keebcu/pics/wristCon.png

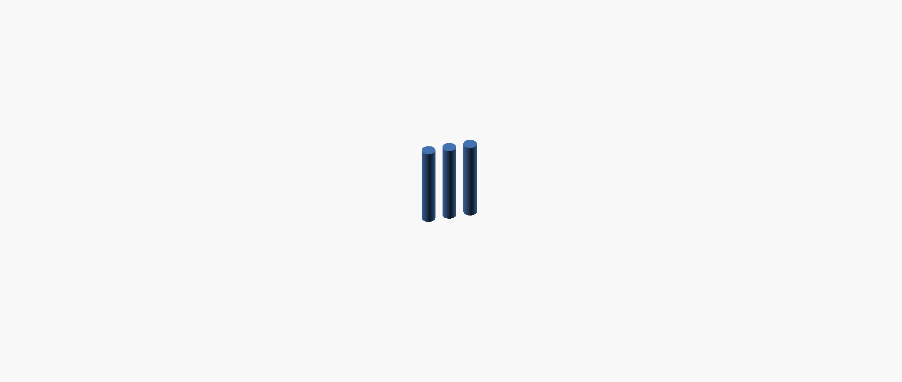
pics/wristCon.png
