andimoto/keebcu/stl/andimotoSmallTKL/andimotoSmallTKL_fRow/andimotoSmallTKL_fRow_mainCaseRight_Teensy2.stl

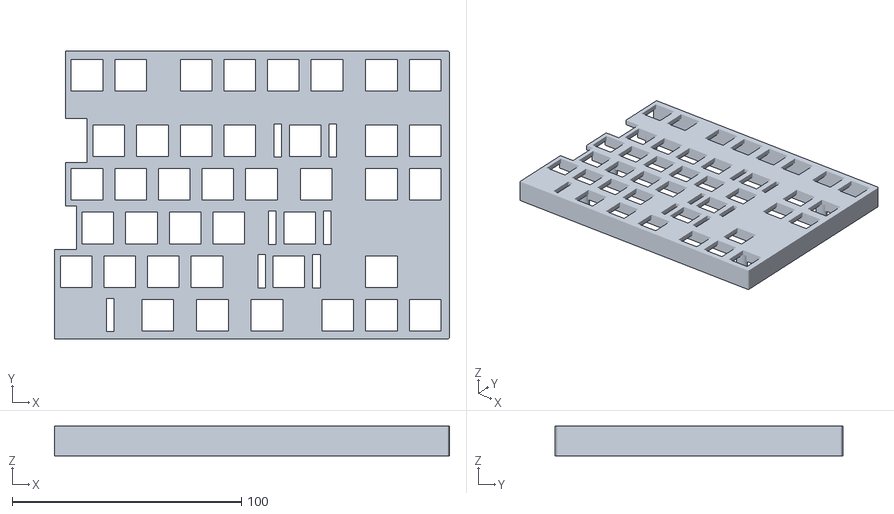
[picture p127: CAD file, 2021-12-27]
stl/andimotoSmallTKL/andimotoSmallTKL_fRow/andimotoSmallTKL_fRow_mainCaseRight_Teensy2.stl
172.4 x 125.8 x 13.0
