andimoto/keebcu/stl/andimotoTKL/andimotoTKL_mainCaseRight.stl

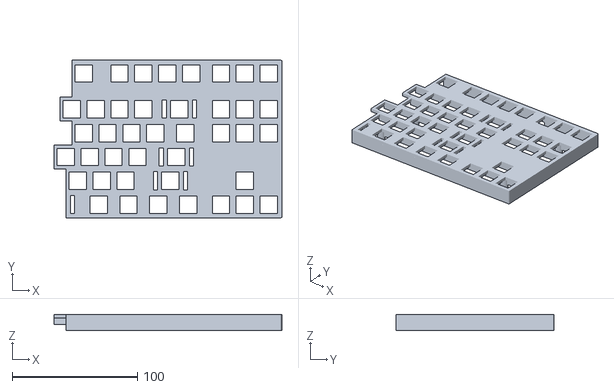
[picture p128: CAD file, 2021-04-02]
stl/andimotoTKL/andimotoTKL_mainCaseRight.stl
182.0 x 125.8 x 13.0
