andimoto/keebcu/stl/andimoto6064/andimoto6064_mainCaseLeft.stl

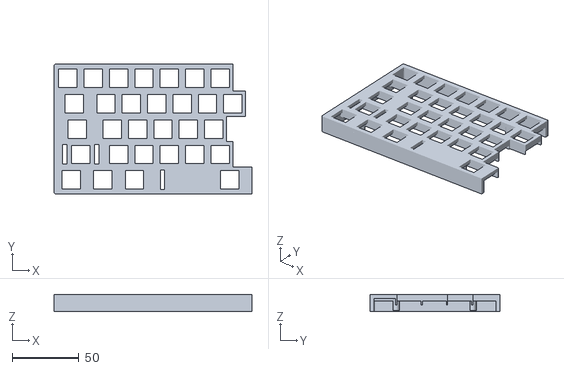
[picture p129: CAD file, 2021-03-24]
stl/andimoto6064/andimoto6064_mainCaseLeft.stl
148.6 x 97.2 x 13.0
