andimoto/keebcu/stl/andimoto7583/andimoto7583-obj-cnc/Unnamed-andimoto7583_mainCase.obj

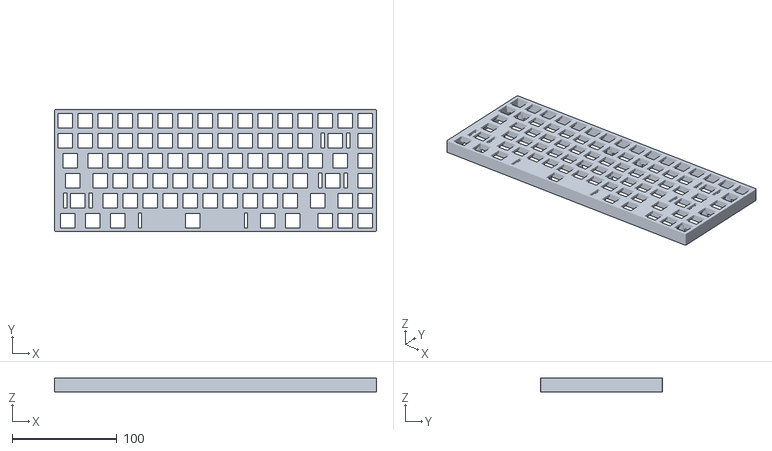
[picture p130: CAD file, 2024-02-24]
stl/andimoto7583/andimoto7583-obj-cnc/Unnamed-andimoto7583_mainCase.obj
306.8 x 116.3 x 13.0
