andimoto/keebcu/stl/andimotoSmallTKL/andimotoSmallTKL_mainCaseRight.stl

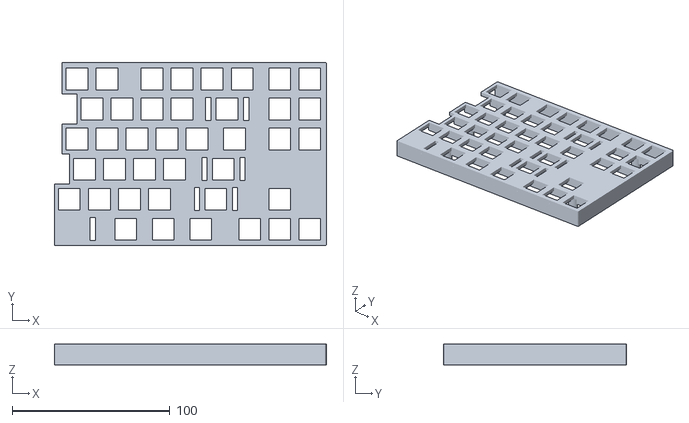
[picture p131: CAD file, 2021-03-21]
stl/andimotoSmallTKL/andimotoSmallTKL_mainCaseRight.stl
172.4 x 116.3 x 13.0
