andimoto/keebcu/stl/andimotoTKLiso/andimotoTKLiso_mainCaseLeft.stl

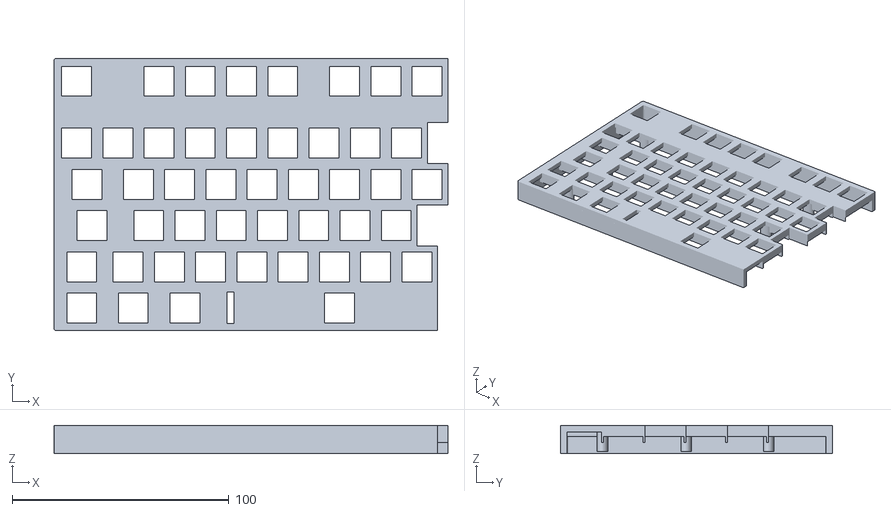
[picture p132: CAD file, 2021-04-02]
stl/andimotoTKLiso/andimotoTKLiso_mainCaseLeft.stl
182.0 x 125.8 x 13.0
