andimoto/keebcu/stl/andimoto6064/andimoto6064_mainCaseRight.stl

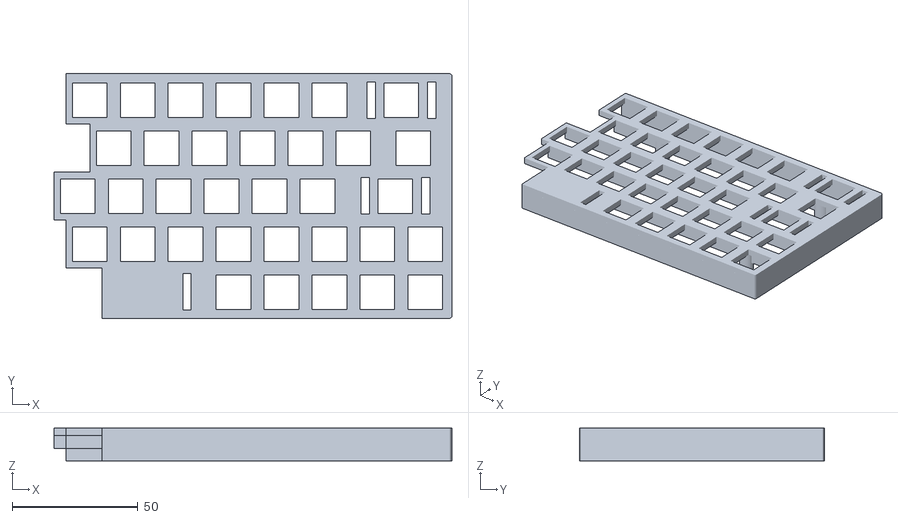
[picture p133: CAD file, 2021-03-24]
stl/andimoto6064/andimoto6064_mainCaseRight.stl
158.2 x 97.2 x 13.0
