andimoto/keebcu/stl/andimoto6064/andimoto6064_mainCase.stl

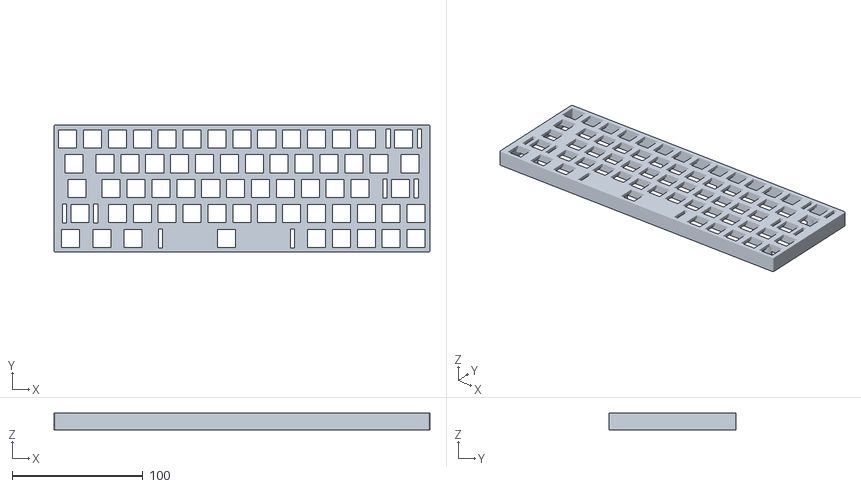
[picture p134: CAD file, 2021-03-24]
stl/andimoto6064/andimoto6064_mainCase.stl
287.8 x 97.2 x 13.0
