andimoto/keebcu/stl/andimoto6061/andimoto6061_keyboardRiser.stl

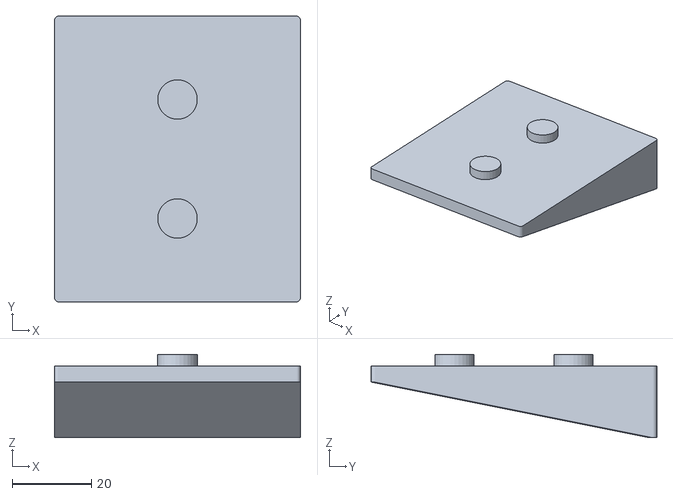
[picture p135: CAD file, 2021-03-21]
stl/andimoto6061/andimoto6061_keyboardRiser.stl
62.0 x 72.0 x 21.0
