andimoto/keebcu/stl/andimoto6064/wristR_287mm.stl

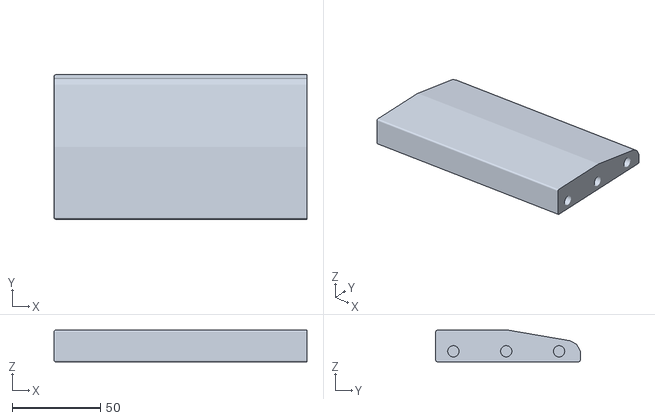
[picture p136: CAD file, 2021-06-02]
stl/andimoto6064/wristR_287mm.stl
143.5 x 82.0 x 18.0
