andimoto/keebcu/stl/andimoto7583/andimoto7583_lid_CNC.stl

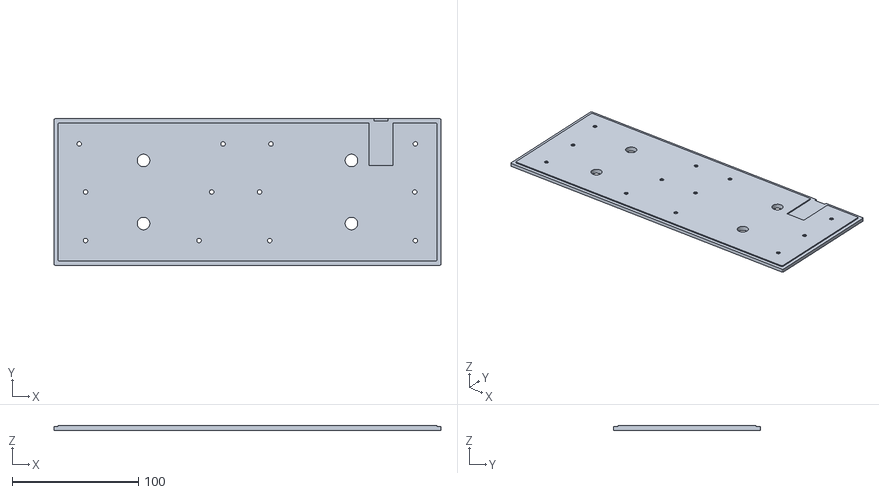
[picture p137: CAD file, 2024-02-24]
stl/andimoto7583/andimoto7583_lid_CNC.stl
306.8 x 116.3 x 4.00
