andimoto/keebcu/stl/andimoto7583/andimoto7584-frame-proMicro/andimoto7584-frameAll-frame-proMicro.stl

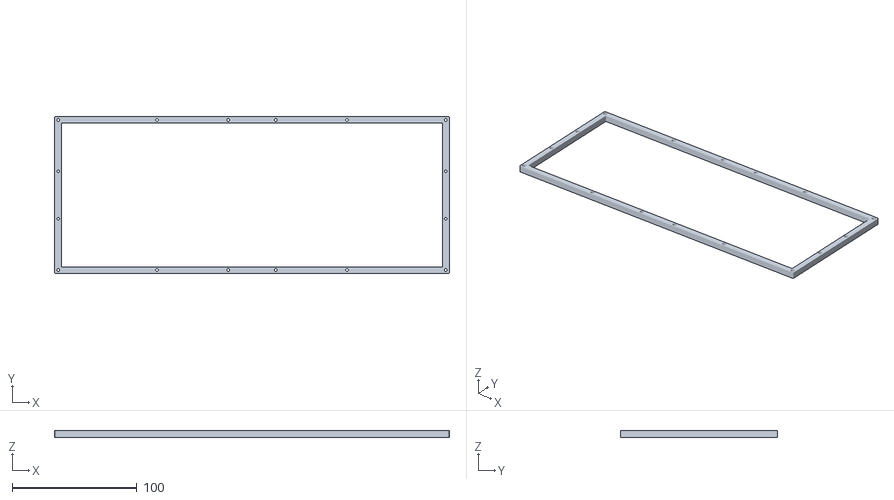
[picture p138: CAD file, 2022-11-19]
stl/andimoto7583/andimoto7584-frame-proMicro/andimoto7584-frameAll-frame-proMicro.stl
316.8 x 126.3 x 6.00
