andimoto/keebcu/stl/andimoto7583/wrist/wrist306L.stl

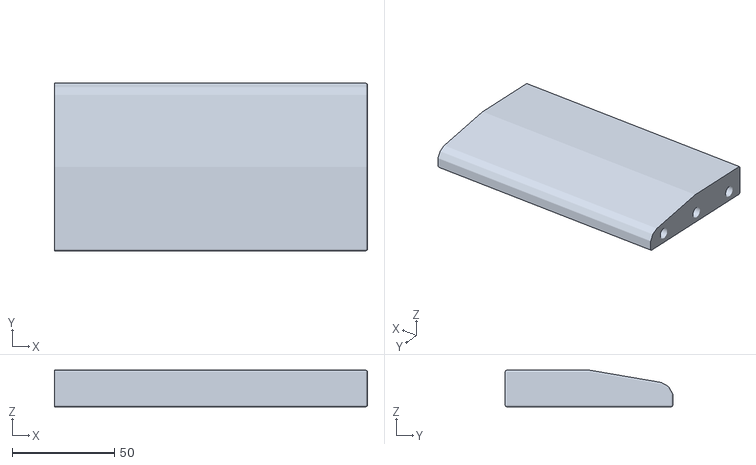
[picture p139: CAD file, 2021-02-12]
stl/andimoto7583/wrist/wrist306L.stl
153.0 x 82.0 x 18.0
