andimoto/keebcu/stl/andimoto75Q1-iso/andimoto75Q1-iso-ALL-frame.stl

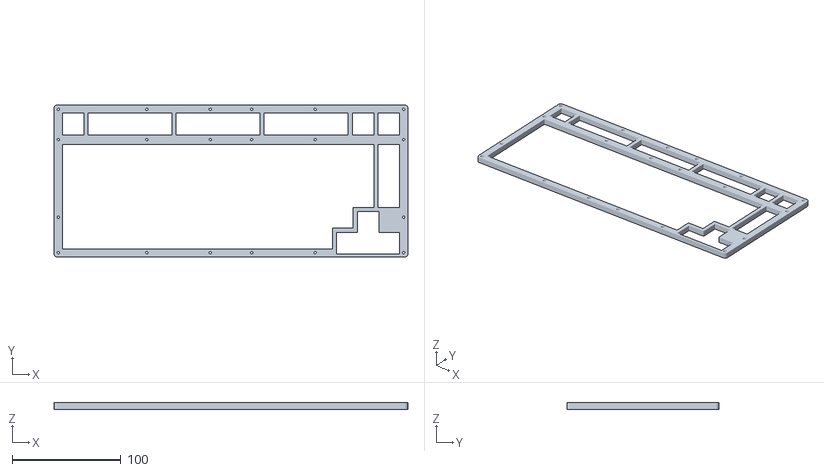
[picture p140: CAD file, 2022-11-04]
stl/andimoto75Q1-iso/andimoto75Q1-iso-ALL-frame.stl
325.6 x 139.8 x 6.00
