andimoto/keebcu/stl/andimoto75Q1/andimoto75Q1-caseR-teensy2.stl

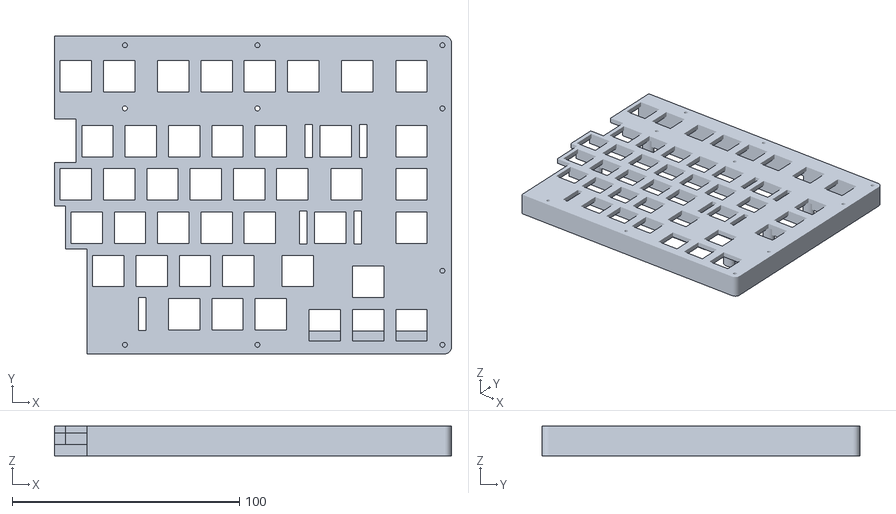
[picture p141: CAD file, 2022-10-18]
stl/andimoto75Q1/andimoto75Q1-caseR-teensy2.stl
174.7 x 139.8 x 13.0
