andimoto/keebcu/stl/andimotoSmallTKL/andimotoSmallTKL_fRow/andimotoSmallTKL_fRow_Riser.stl

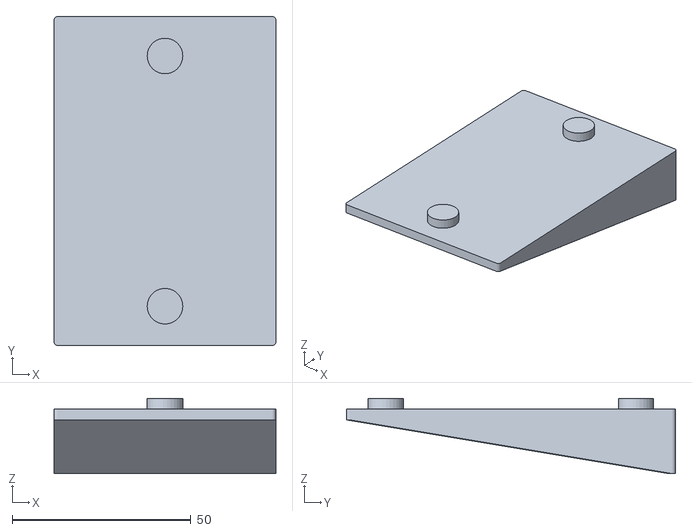
[picture p142: CAD file, 2021-12-27]
stl/andimotoSmallTKL/andimotoSmallTKL_fRow/andimotoSmallTKL_fRow_Riser.stl
62.0 x 92.0 x 21.0
