andimoto/keebcu/stl/andimotoSmallTKL/wrist-rest/wrist_smallTKL_Right.stl

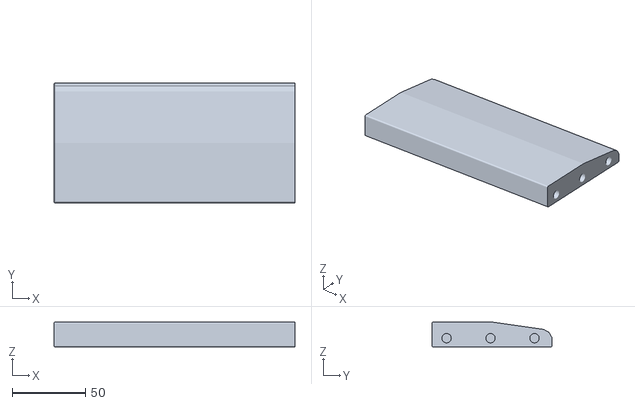
[picture p143: CAD file, 2021-02-12]
stl/andimotoSmallTKL/wrist-rest/wrist_smallTKL_Right.stl
164.5 x 82.0 x 17.0
