andimoto/keebcu/stl/andimotoSmallTKLiso/andimotoSmallTKLiso_ALL-Case-Teensy2.stl

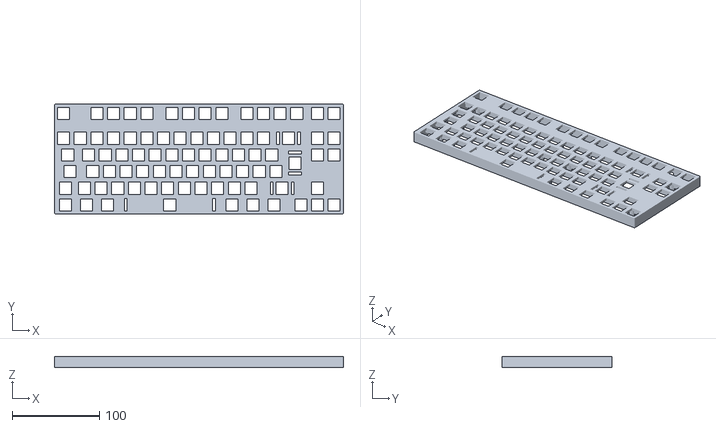
[picture p144: CAD file, 2022-10-18]
stl/andimotoSmallTKLiso/andimotoSmallTKLiso_ALL-Case-Teensy2.stl
330.6 x 125.8 x 13.0
