andimoto/keebcu/stl/andimotoSmallTKLiso/wristRest/wrist330L.stl

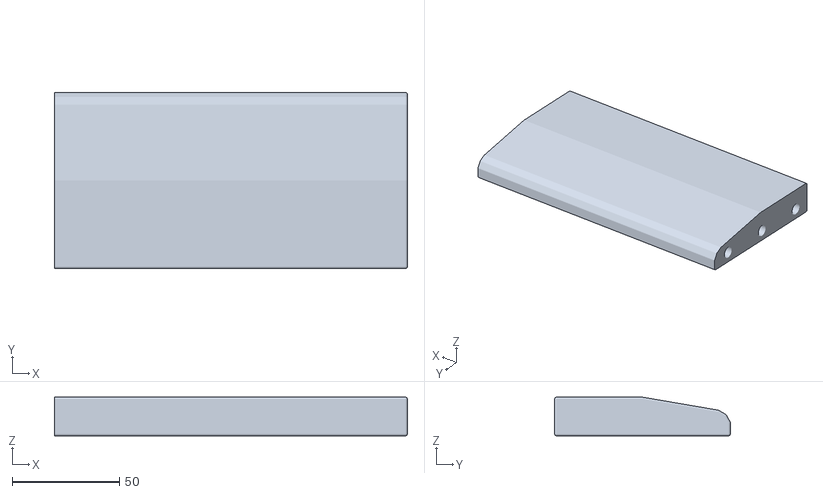
[picture p145: CAD file, 2021-03-13]
stl/andimotoSmallTKLiso/wristRest/wrist330L.stl
164.5 x 82.0 x 18.0
