andimoto/keebcu/stl/andimotoTKL/andimotoTKL_lidR.stl

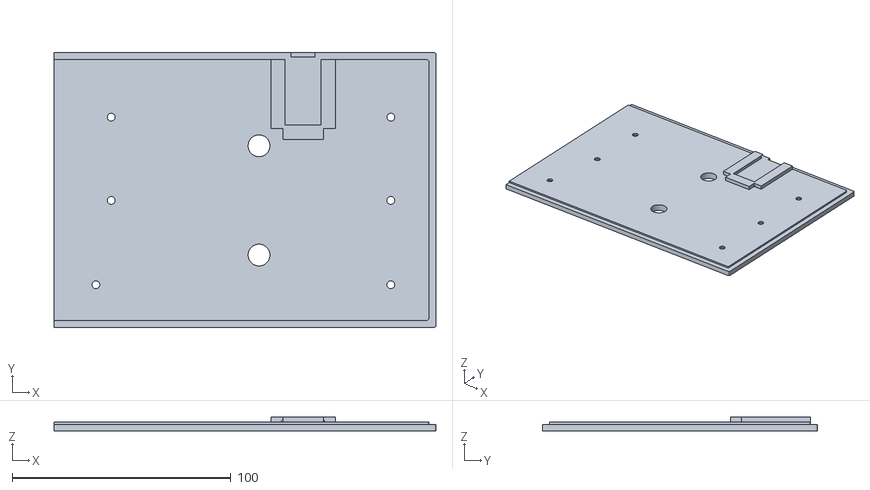
[picture p146: CAD file, 2021-04-02]
stl/andimotoTKL/andimotoTKL_lidR.stl
174.8 x 125.8 x 6.30
