andimoto/keebcu/stl/andimotoTKL/wrist/wrist358L.stl

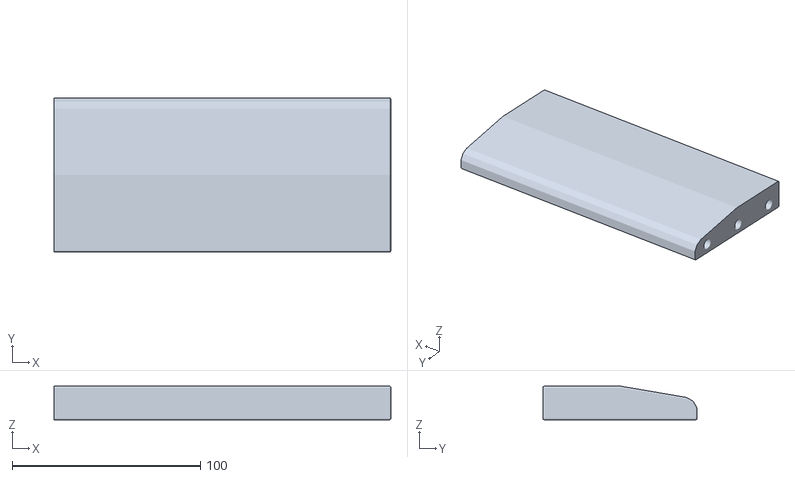
[picture p147: CAD file, 2021-03-13]
stl/andimotoTKL/wrist/wrist358L.stl
179.0 x 82.0 x 18.0
