andimoto/keebcu/stl/andimotoTKLiso/andimotoTKLiso_keyboardRiser.stl

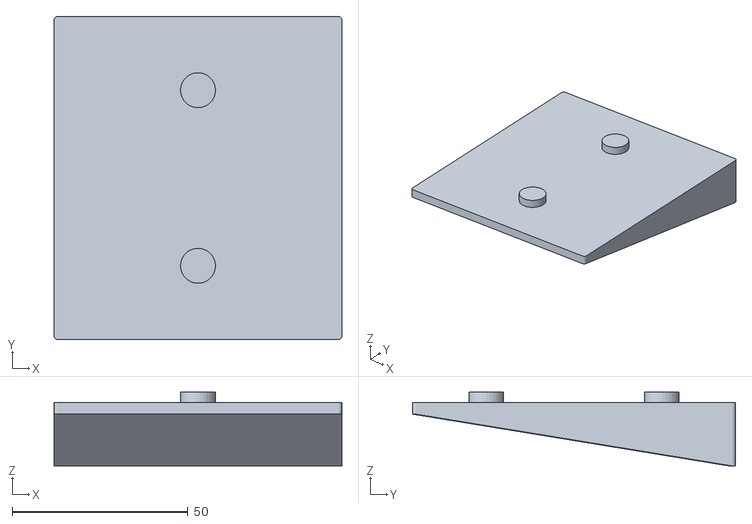
[picture p148: CAD file, 2021-04-02]
stl/andimotoTKLiso/andimotoTKLiso_keyboardRiser.stl
82.0 x 92.0 x 21.0
