andimoto/keebcu/stl/macropad/macropad_lid_5x2_ProMicro.stl

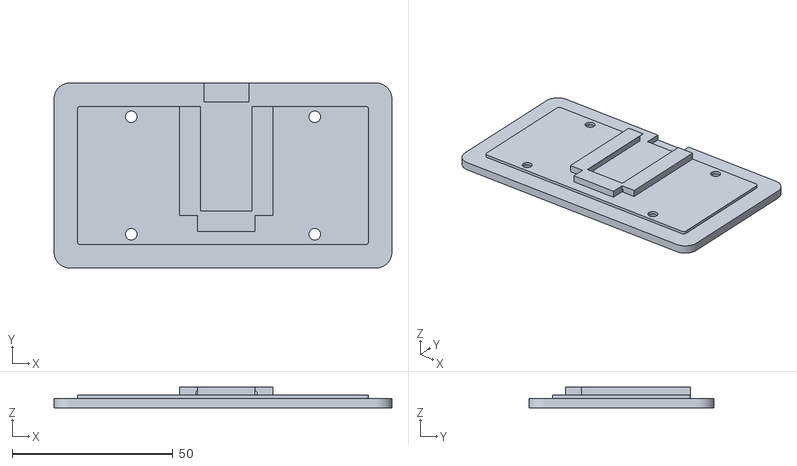
[picture p149: CAD file, 2021-09-02]
stl/macropad/macropad_lid_5x2_ProMicro.stl
105.2 x 57.6 x 6.50
