andimoto/keebcu/stl/numpad/numpad_riser.stl

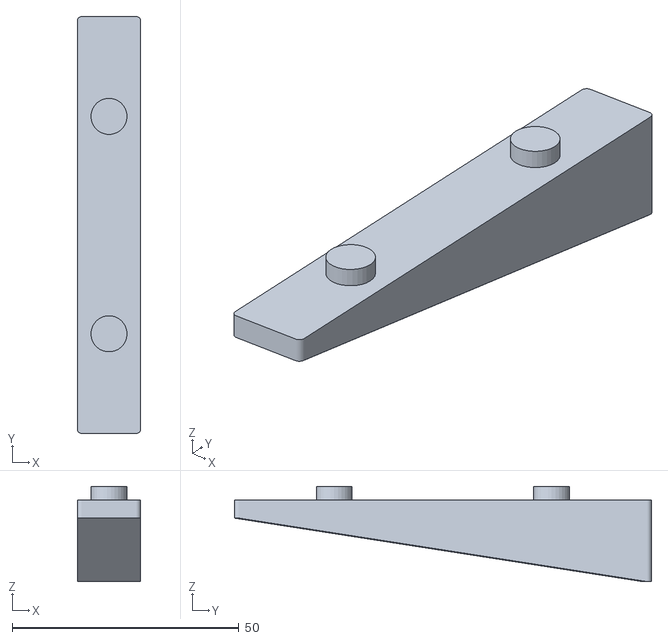
[picture p150: CAD file, 2021-12-28]
stl/numpad/numpad_riser.stl
14.0 x 92.0 x 21.0
