andimoto/keebcu/stl/wrist36L.stl

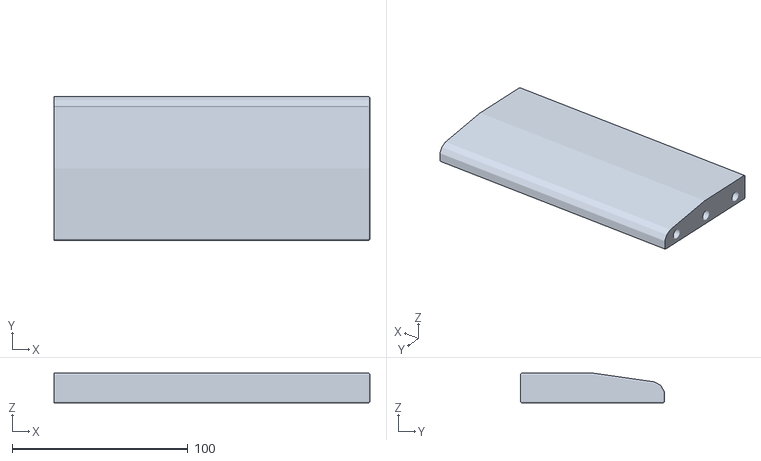
[picture p151: CAD file, 2021-02-12]
stl/wrist36L.stl
180.0 x 82.0 x 17.0
