andimoto/keebcu/stl/andimoto7583/andimoto7583-obj-cnc/Unnamed-andimoto7583_lidR_CNC.obj

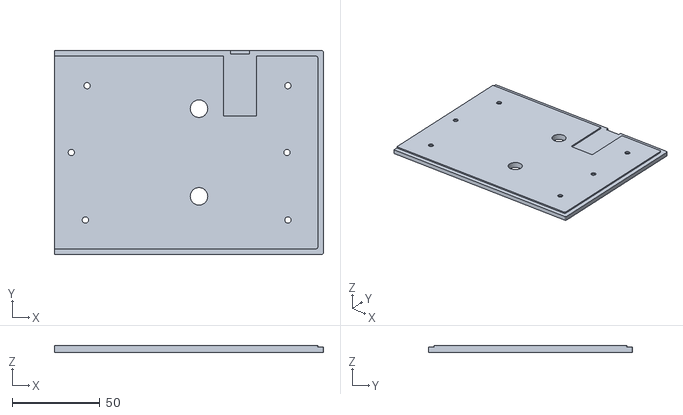
[picture p152: CAD file, 2024-02-24]
stl/andimoto7583/andimoto7583-obj-cnc/Unnamed-andimoto7583_lidR_CNC.obj
153.4 x 116.3 x 4.00
