andimoto/keebcu/stl/andimoto75Q1-iso/andimoto75Q1-iso-ALL-Case-Teensy2.stl

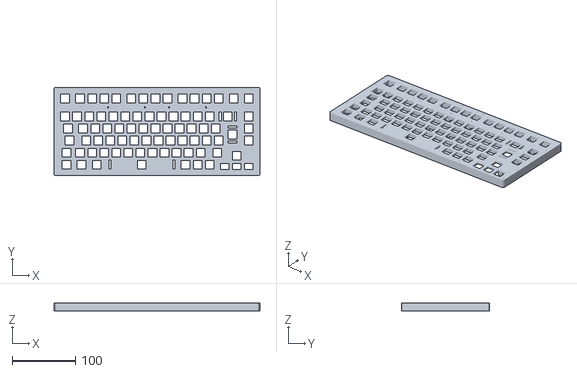
[picture p154: CAD file, 2022-11-04]
stl/andimoto75Q1-iso/andimoto75Q1-iso-ALL-Case-Teensy2.stl
325.6 x 139.8 x 13.0
