andimoto/keebcu/stl/andimoto75Q1/andimoto75Q1-caseL-teensy2.stl

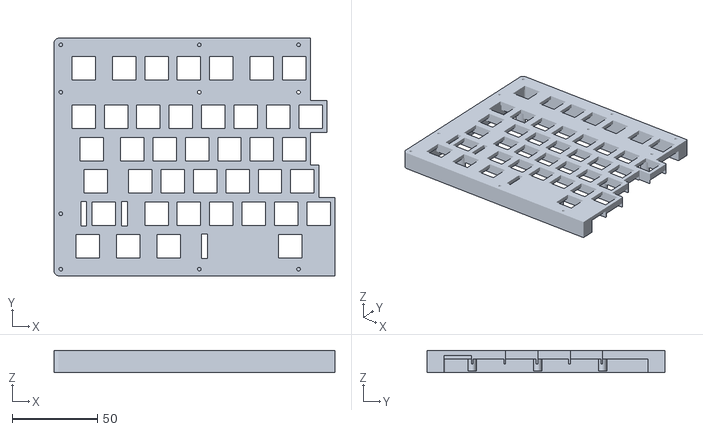
[picture p155: CAD file, 2022-10-18]
stl/andimoto75Q1/andimoto75Q1-caseL-teensy2.stl
165.2 x 139.8 x 13.0
