andimoto/keebcu/stl/andimotoSmallTKL/andimotoSmallTKL_fRow/andimotoSmallTKL_fRow_LidR_Teensy2.stl

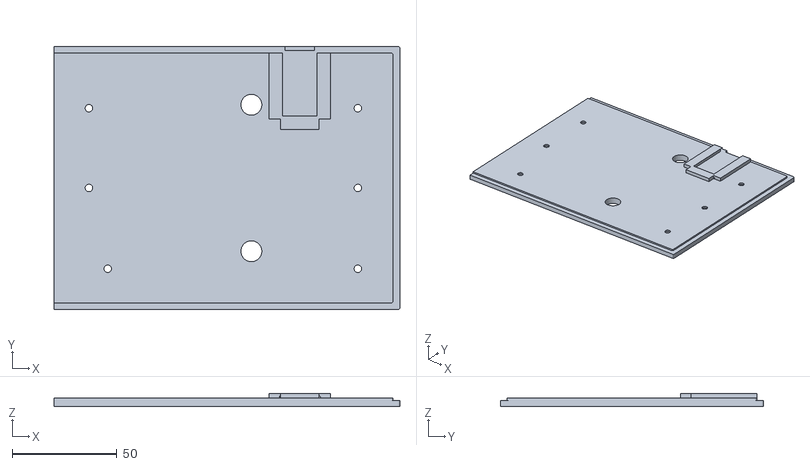
[picture p156: CAD file, 2021-12-27]
stl/andimotoSmallTKL/andimotoSmallTKL_fRow/andimotoSmallTKL_fRow_LidR_Teensy2.stl
165.3 x 125.8 x 6.30
