andimoto/keebcu/stl/andimotoSmallTKL/andimotoSmallTKL_lidR.stl

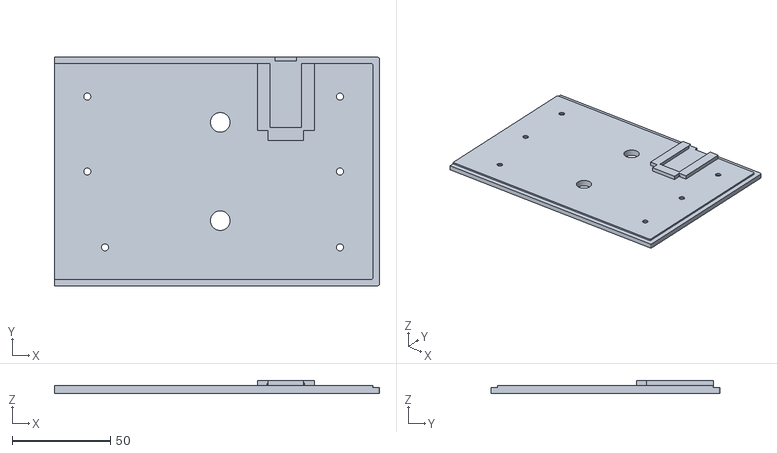
[picture p157: CAD file, 2021-03-21]
stl/andimotoSmallTKL/andimotoSmallTKL_lidR.stl
165.3 x 116.3 x 6.50
