andimoto/keebcu/stl/andimotoSmallTKLiso/andimotoSmallTKLiso_lidL.stl

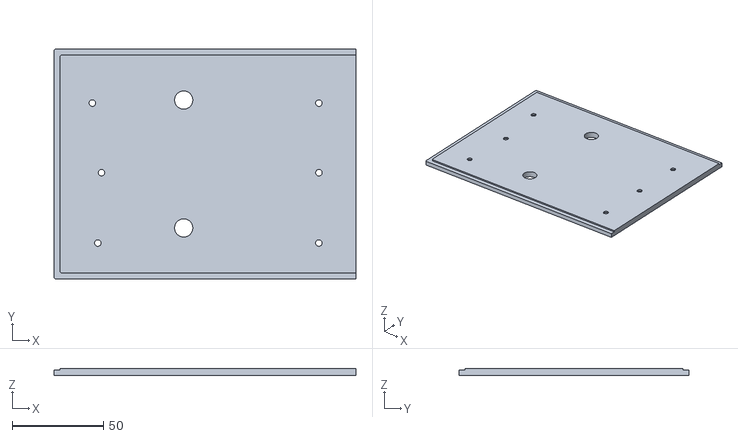
[picture p158: CAD file, 2022-10-18]
stl/andimotoSmallTKLiso/andimotoSmallTKLiso_lidL.stl
165.3 x 125.8 x 4.00
