andimoto/keebcu/stl/andimotoSmallTKLiso/wristRest/wristConnectors.stl

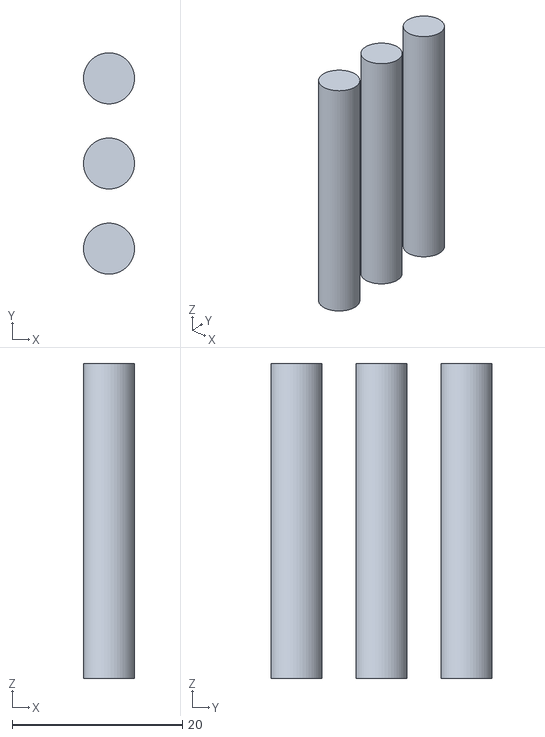
[picture p159: CAD file, 2021-03-13]
stl/andimotoSmallTKLiso/wristRest/wristConnectors.stl
6.00 x 26.0 x 37.0
