andimoto/keebcu/stl/andimotoTKLiso/andimotoTKLiso_lidL.stl

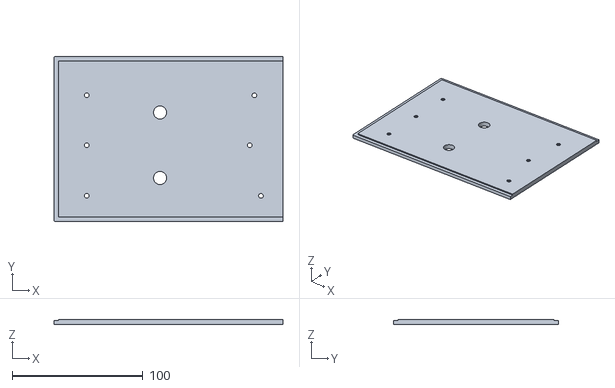
[picture p160: CAD file, 2021-04-02]
stl/andimotoTKLiso/andimotoTKLiso_lidL.stl
174.8 x 125.8 x 4.00
