andimoto/keebcu/stl/macropad/macropad_5x2_ProMicro.stl

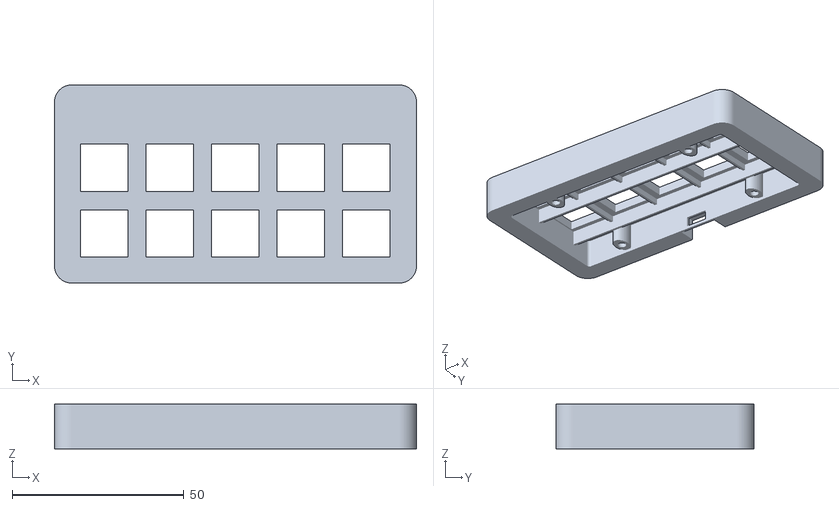
[picture p161: CAD file, 2021-08-31]
stl/macropad/macropad_5x2_ProMicro.stl
105.2 x 57.6 x 13.0
