andimoto/keebcu/stl/numpad/numpad_case_proMicro.stl

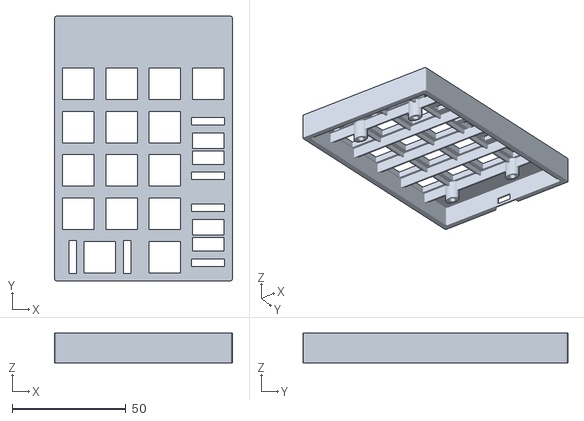
[picture p162: CAD file, 2021-12-07]
stl/numpad/numpad_case_proMicro.stl
78.2 x 116.3 x 13.0
