andimoto/keebcu/stl/wristConnector.stl

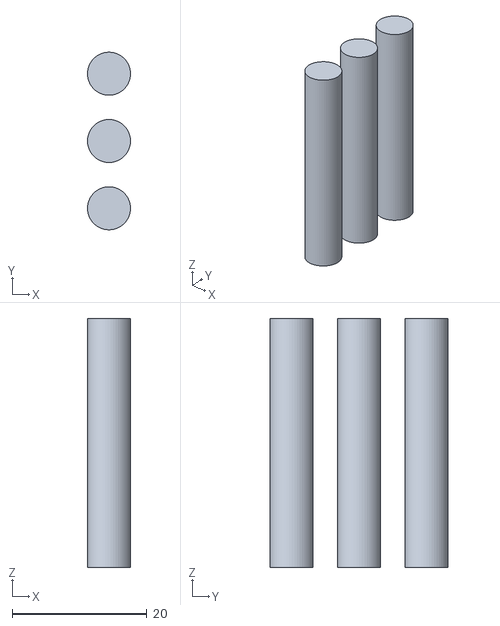
[picture p163: CAD file, 2021-02-12]
stl/wristConnector.stl
6.40 x 26.4 x 37.0
