andimoto/keebcu/stl/andimoto6061/andimoto6061_lid.stl

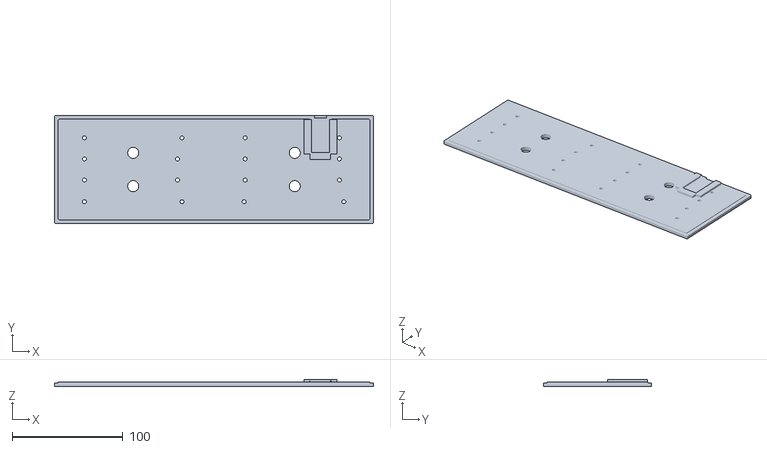
[picture p164: CAD file, 2021-03-21]
stl/andimoto6061/andimoto6061_lid.stl
287.8 x 97.2 x 6.30
