andimoto/keebcu/stl/andimoto6064/keebCase6064.stl

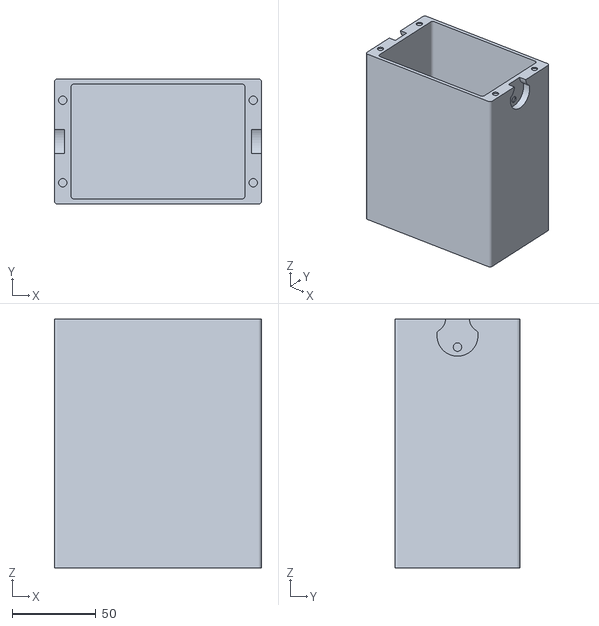
[picture p165: CAD file, 2021-06-02]
stl/andimoto6064/keebCase6064.stl
124.0 x 75.0 x 149.0
