andimoto/keebcu/stl/andimoto7583/andimoto7584-frame-proMicro/andimoto7584-caseAll-frame-proMicro.stl

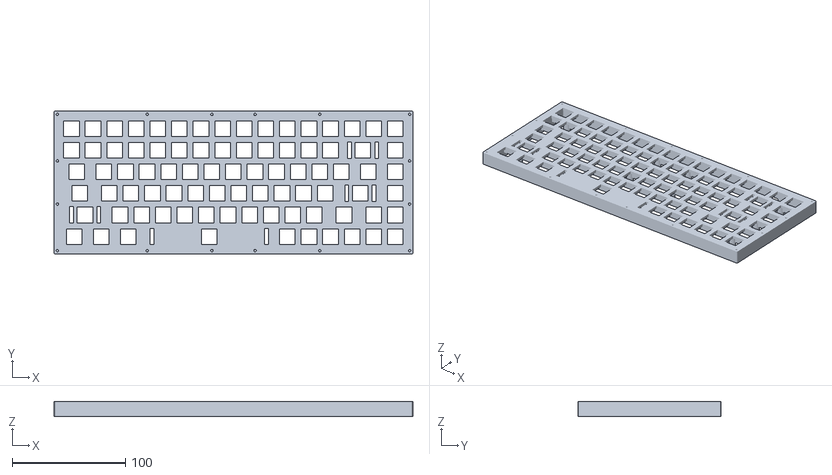
[picture p166: CAD file, 2022-11-19]
stl/andimoto7583/andimoto7584-frame-proMicro/andimoto7584-caseAll-frame-proMicro.stl
316.8 x 126.3 x 13.0
