andimoto/keebcu/stl/andimoto7583/wrist/wristConnectors.stl

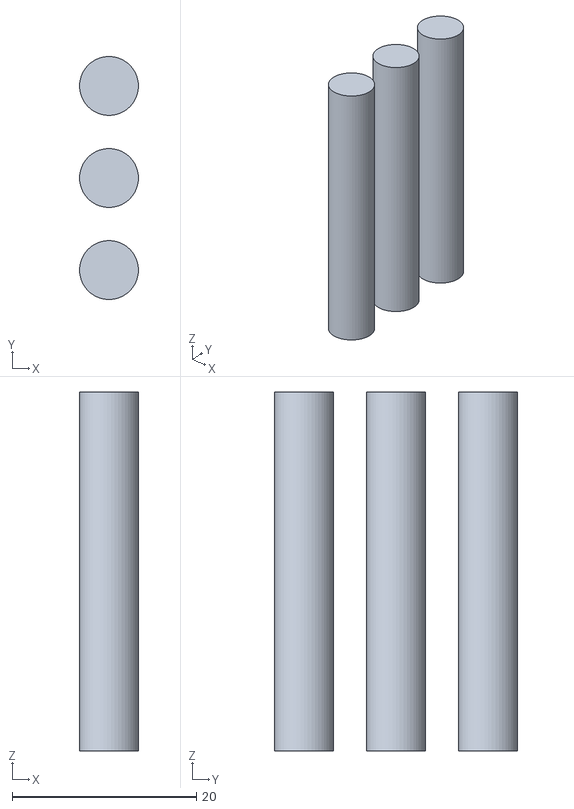
[picture p167: CAD file, 2021-02-12]
stl/andimoto7583/wrist/wristConnectors.stl
6.40 x 26.4 x 39.0
