andimoto/keebcu/stl/andimoto75Q1-iso/andimoto75Q1-iso-ALL-Lid-Teensy2.stl

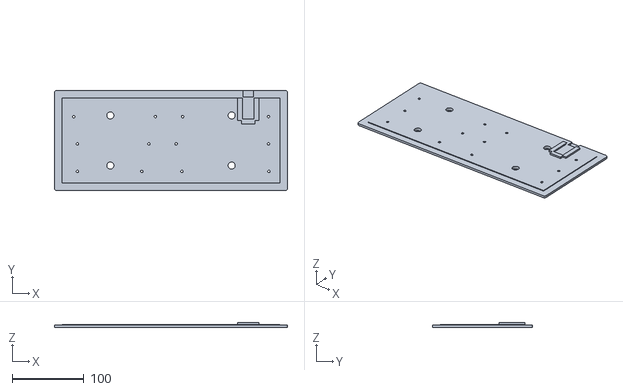
[picture p168: CAD file, 2022-11-04]
stl/andimoto75Q1-iso/andimoto75Q1-iso-ALL-Lid-Teensy2.stl
325.6 x 139.8 x 6.30
