andimoto/keebcu/stl/andimotoSmallTKL/andimotoSmallTKL_lid.stl

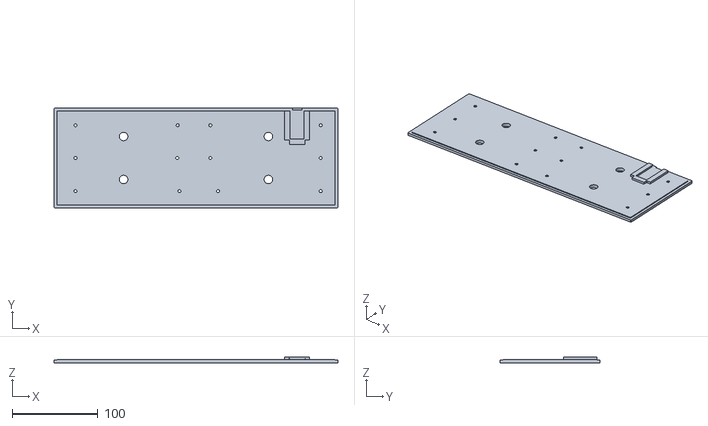
[picture p170: CAD file, 2021-03-21]
stl/andimotoSmallTKL/andimotoSmallTKL_lid.stl
330.6 x 116.3 x 6.50
