andimoto/keebcu/stl/andimotoTKL/andimotoTKL_lid.stl

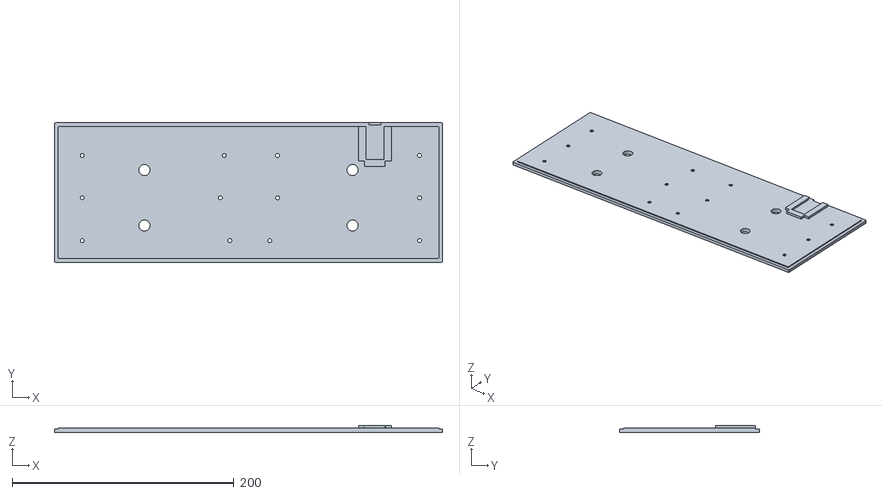
[picture p171: CAD file, 2021-04-02]
stl/andimotoTKL/andimotoTKL_lid.stl
349.7 x 125.8 x 6.30
