andimoto/keebcu/stl/numpad/numpad_lid_proMicro.stl

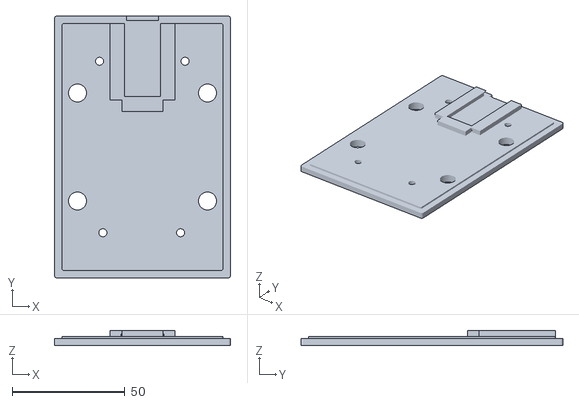
[picture p172: CAD file, 2021-12-07]
stl/numpad/numpad_lid_proMicro.stl
78.2 x 116.3 x 6.50
