andimoto/keebcu/stl/andimoto6064/andimoto6064_lidR.stl

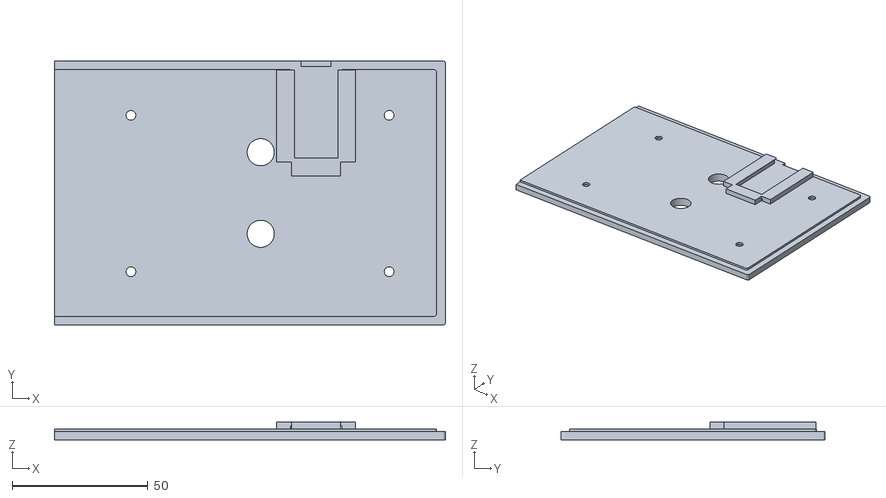
[picture p173: CAD file, 2021-03-24]
stl/andimoto6064/andimoto6064_lidR.stl
143.9 x 97.2 x 6.50
