andimoto/keebcu/stl/andimoto7583/andimoto7584-frame-proMicro/andimoto7584-caseRight-frame-proMicro.stl

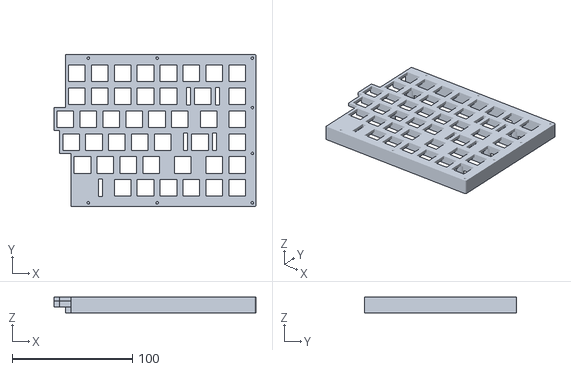
[picture p174: CAD file, 2022-11-19]
stl/andimoto7583/andimoto7584-frame-proMicro/andimoto7584-caseRight-frame-proMicro.stl
167.9 x 126.3 x 13.0
