andimoto/keebcu/stl/andimoto75Q1/andimoto75Q1-riser.stl

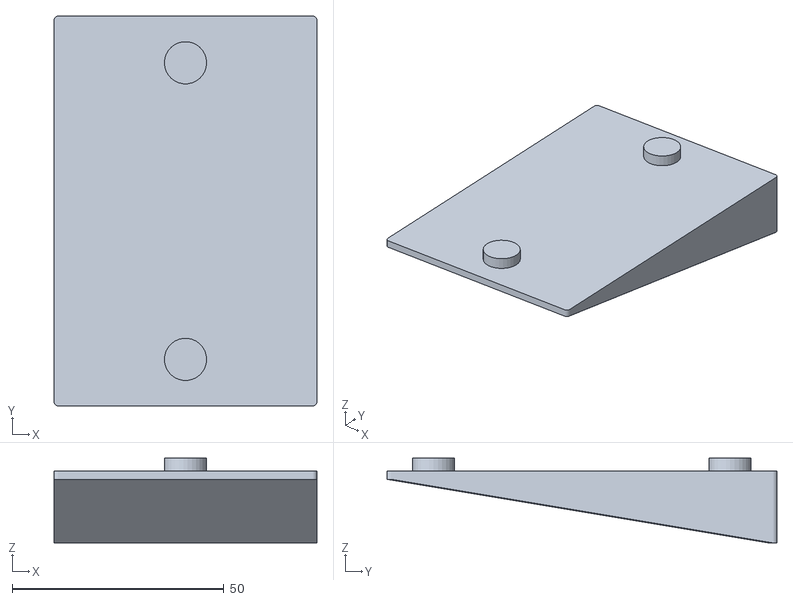
[picture p175: CAD file, 2022-10-18]
stl/andimoto75Q1/andimoto75Q1-riser.stl
62.0 x 92.0 x 20.0
