andimoto/keebcu/stl/andimotoSmallTKLiso/andimotoSmallTKLiso_lidR-ProMicro.stl

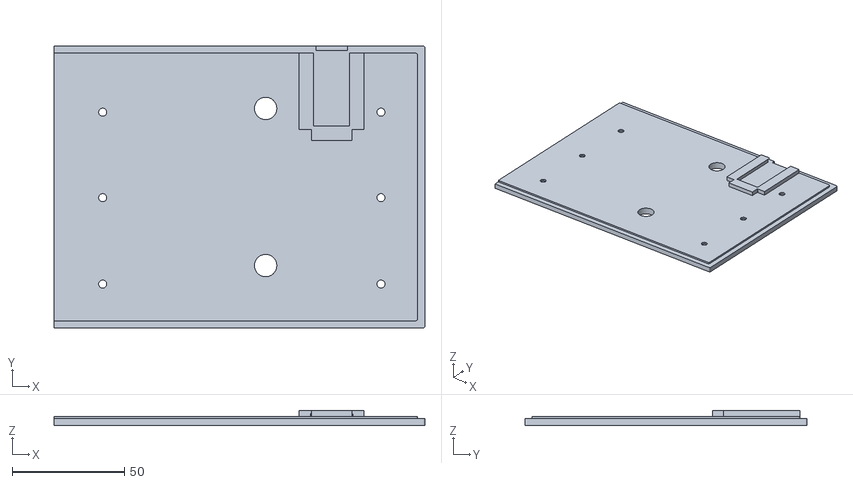
[picture p176: CAD file, 2022-10-18]
stl/andimotoSmallTKLiso/andimotoSmallTKLiso_lidR-ProMicro.stl
165.3 x 125.8 x 6.50
