andimoto/keebcu/stl/andimoto6064/andimoto6064_lid.stl

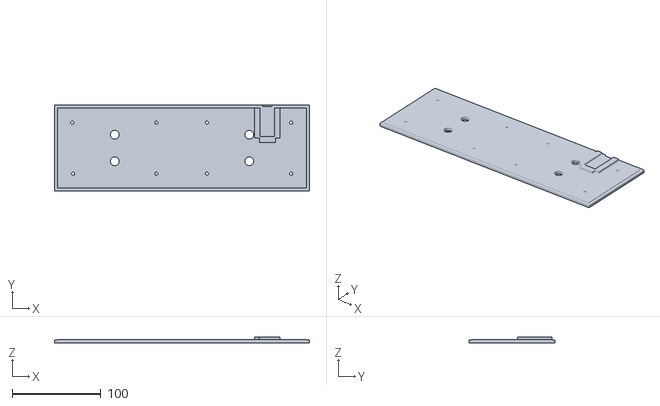
[picture p177: CAD file, 2021-03-24]
stl/andimoto6064/andimoto6064_lid.stl
287.8 x 97.2 x 6.50
