andimoto/keebcu/stl/andimoto7583/andimoto7583_lidR.stl

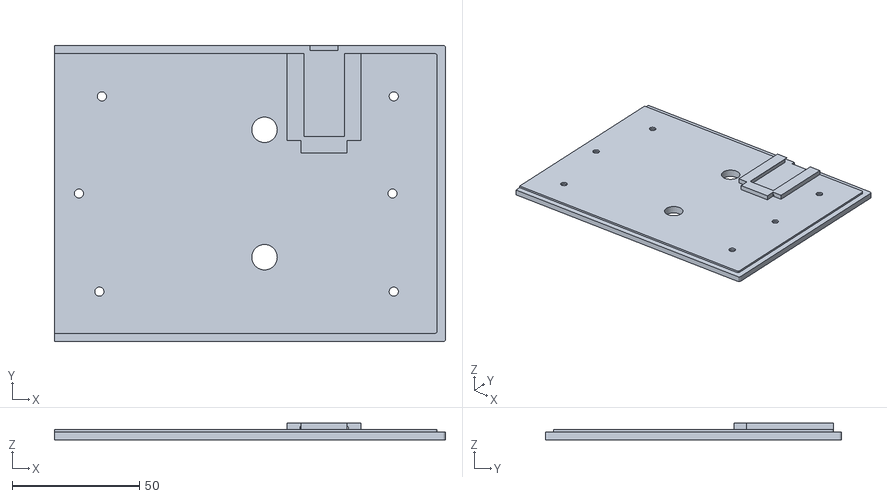
[picture p178: CAD file, 2021-03-21]
stl/andimoto7583/andimoto7583_lidR.stl
153.4 x 116.3 x 6.50
