andimoto/keebcu/stl/andimoto7583/andimoto7584-frame-proMicro/andimoto7584-riser.stl

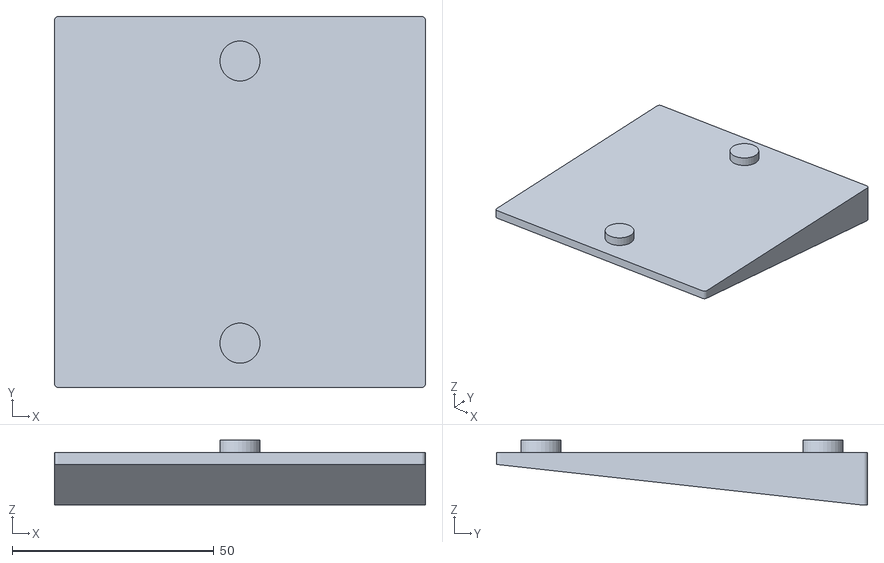
[picture p179: CAD file, 2022-11-19]
stl/andimoto7583/andimoto7584-frame-proMicro/andimoto7584-riser.stl
92.0 x 92.0 x 16.0
