andimoto/keebcu/stl/andimoto75Q1/andimoto75Q1-lidL-teensy2.stl

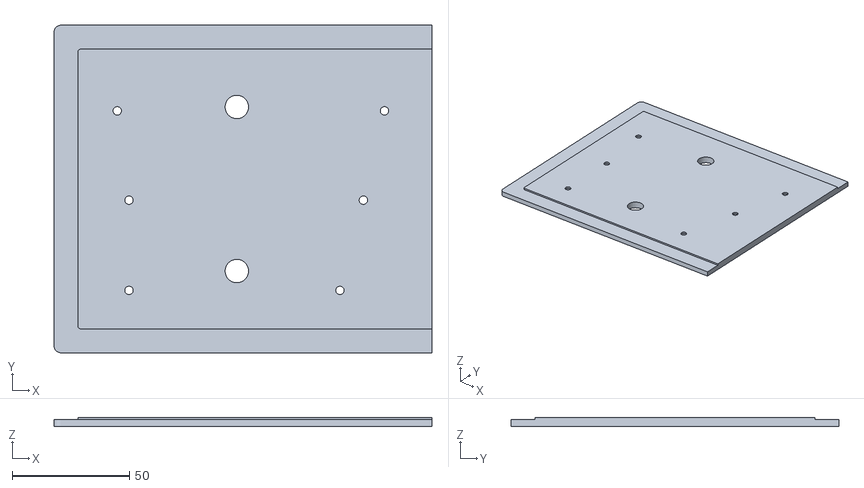
[picture p180: CAD file, 2022-10-18]
stl/andimoto75Q1/andimoto75Q1-lidL-teensy2.stl
161.3 x 139.8 x 4.00
