andimoto/keebcu/stl/andimotoSmallTKL/andimotoSmallTKL_lidL.stl

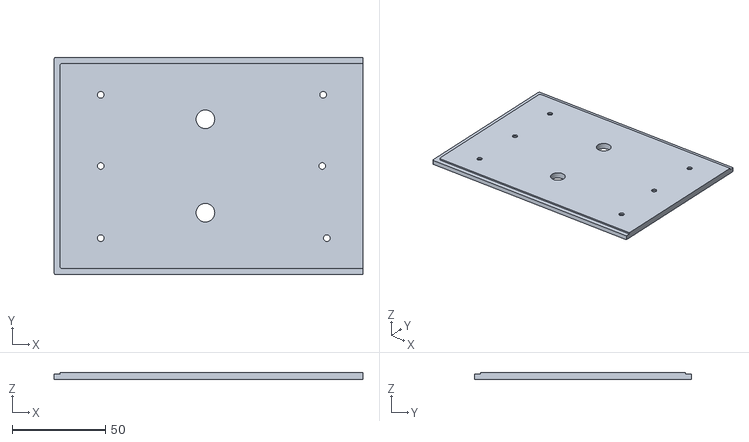
[picture p181: CAD file, 2021-03-21]
stl/andimotoSmallTKL/andimotoSmallTKL_lidL.stl
165.3 x 116.3 x 4.00
