andimoto/keebcu/stl/andimoto6061/andimoto6061_lidL.stl

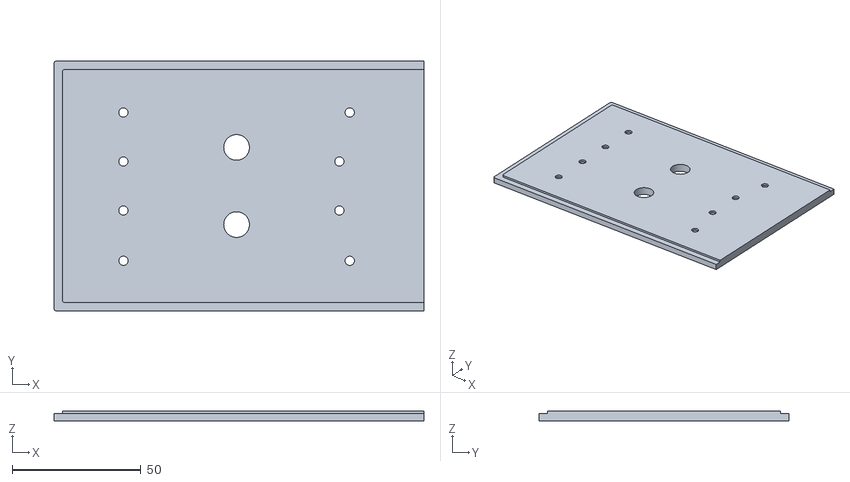
[picture p182: CAD file, 2021-03-21]
stl/andimoto6061/andimoto6061_lidL.stl
143.9 x 97.2 x 4.00
