andimoto/keebcu/stl/andimoto7583/andimoto7583_lid.stl

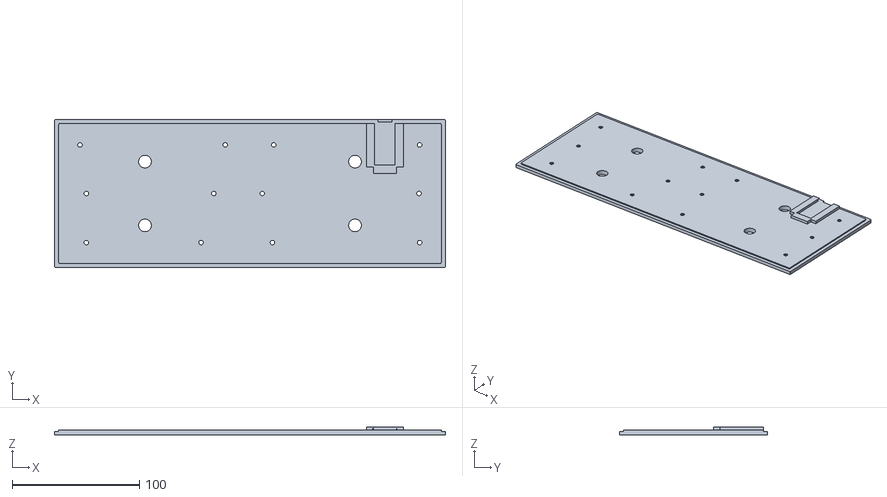
[picture p183: CAD file, 2021-03-21]
stl/andimoto7583/andimoto7583_lid.stl
306.8 x 116.3 x 6.50
