andimoto/keebcu/stl/andimoto7583/andimoto7584-frame-proMicro/andimoto7584-frameRight-frame-proMicro.stl

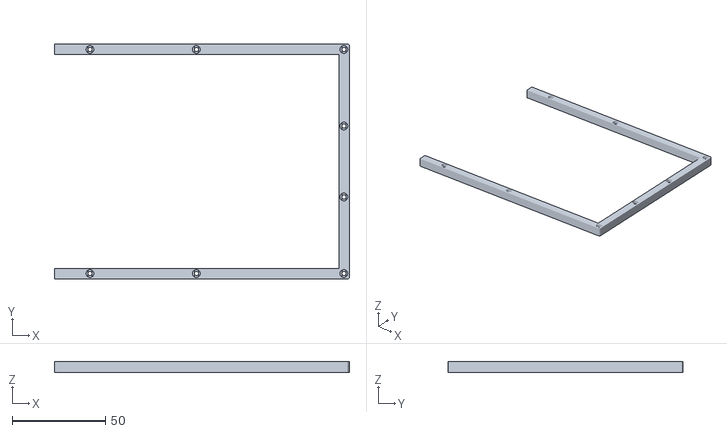
[picture p184: CAD file, 2022-11-19]
stl/andimoto7583/andimoto7584-frame-proMicro/andimoto7584-frameRight-frame-proMicro.stl
158.4 x 126.3 x 6.00
