andimoto/keebcu/stl/andimoto75Q1/andimoto75Q1-lidRteensy2.stl

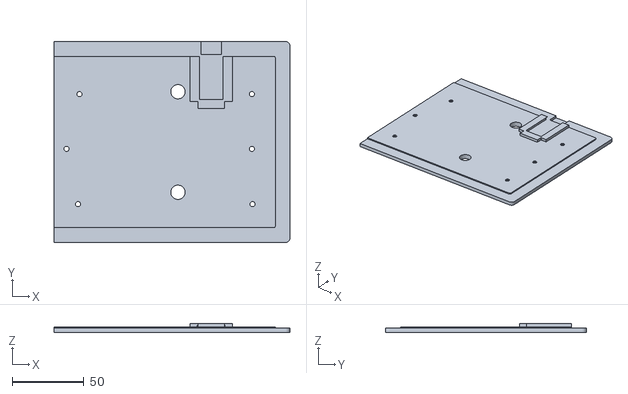
[picture p185: CAD file, 2022-10-18]
stl/andimoto75Q1/andimoto75Q1-lidRteensy2.stl
164.3 x 139.8 x 6.30
