andimoto/keebcu/stl/andimoto6061/andimoto6061_lidR.stl

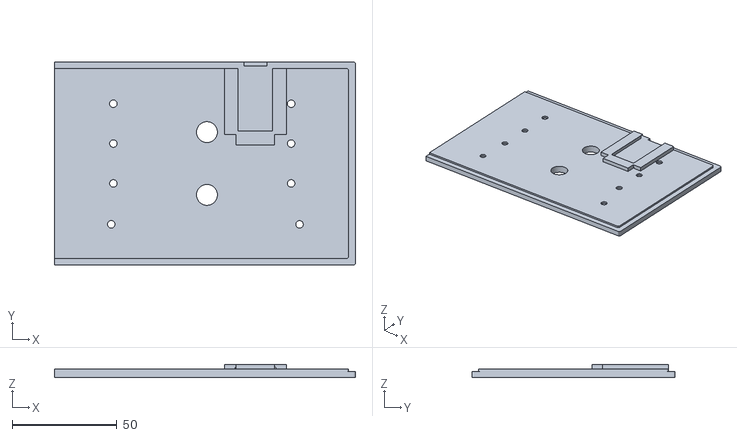
[picture p186: CAD file, 2021-03-21]
stl/andimoto6061/andimoto6061_lidR.stl
143.9 x 97.2 x 6.30
