andimoto/keebcu/stl/andimoto7583/andimoto7584-frame-proMicro/andimoto7584-caseLeft-frame-proMicro.stl

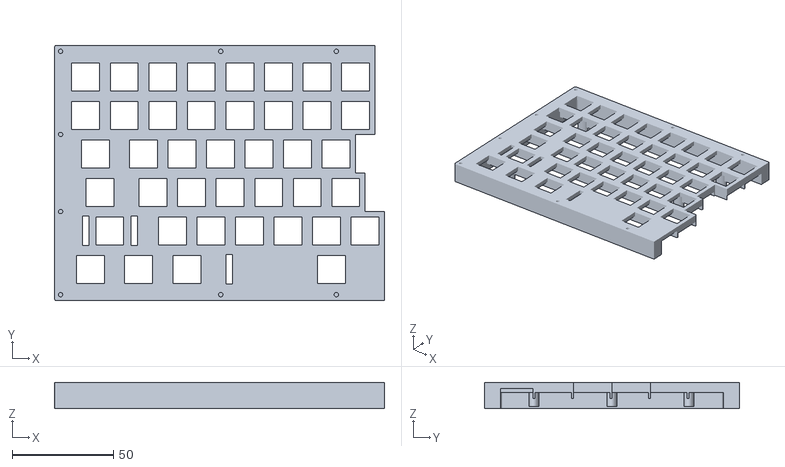
[picture p187: CAD file, 2022-11-19]
stl/andimoto7583/andimoto7584-frame-proMicro/andimoto7584-caseLeft-frame-proMicro.stl
163.2 x 126.3 x 13.0
