andimoto/keebcu/stl/andimoto75Q1/andimoto75Q1-frameL.stl

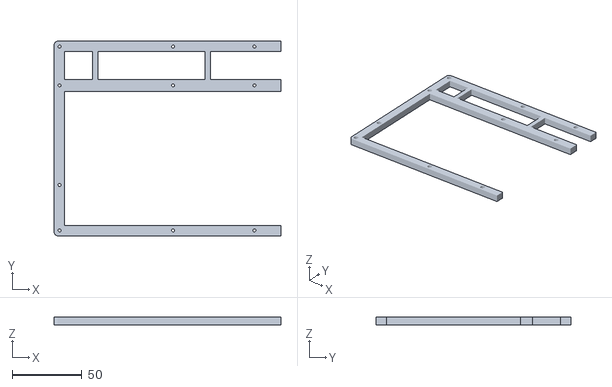
[picture p188: CAD file, 2022-10-18]
stl/andimoto75Q1/andimoto75Q1-frameL.stl
162.8 x 139.8 x 6.00
