andimoto/keebcu/stl/andimoto6064/andimoto6064_keyboardRiser.stl

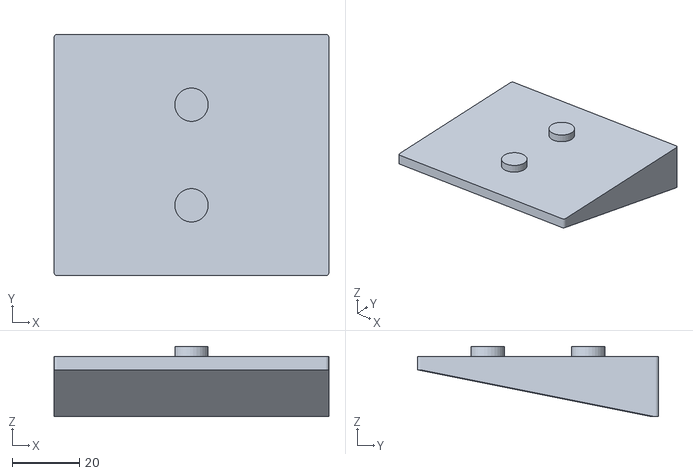
[picture p189: CAD file, 2021-03-24]
stl/andimoto6064/andimoto6064_keyboardRiser.stl
82.0 x 72.0 x 21.0
