andimoto/keebcu/stl/andimotoSmallTKLiso/andimotoSmallTKLiso_ALL-Lid-Teensy2.stl

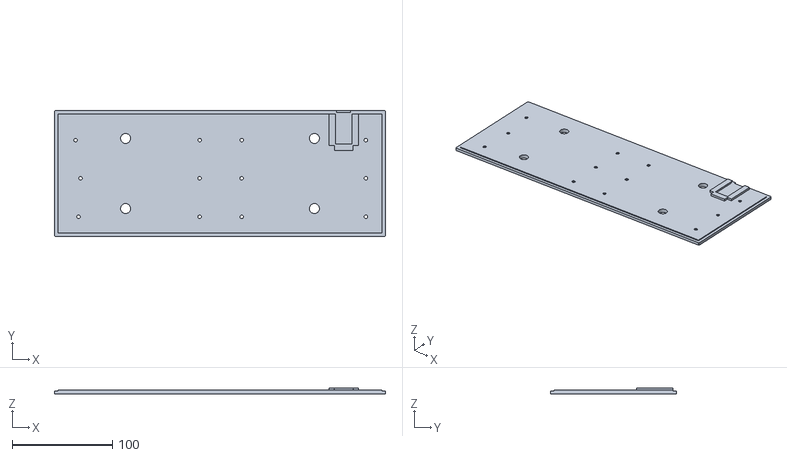
[picture p190: CAD file, 2022-10-18]
stl/andimotoSmallTKLiso/andimotoSmallTKLiso_ALL-Lid-Teensy2.stl
330.6 x 125.8 x 6.30
