andimoto/keebcu/stl/andimoto7583/andimoto7584-frame-proMicro/andimoto7584-lidRight-frame-proMicro.stl

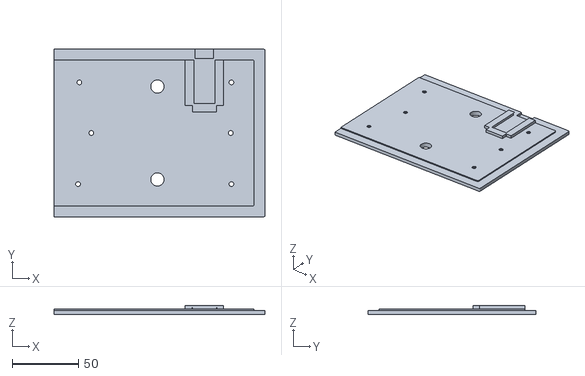
[picture p191: CAD file, 2022-11-19]
stl/andimoto7583/andimoto7584-frame-proMicro/andimoto7584-lidRight-frame-proMicro.stl
158.9 x 126.3 x 6.50
