andimoto/keebcu/stl/andimoto7583/andimoto7584-frame-proMicro/andimoto7584-lidLeft-frame-proMicro.stl

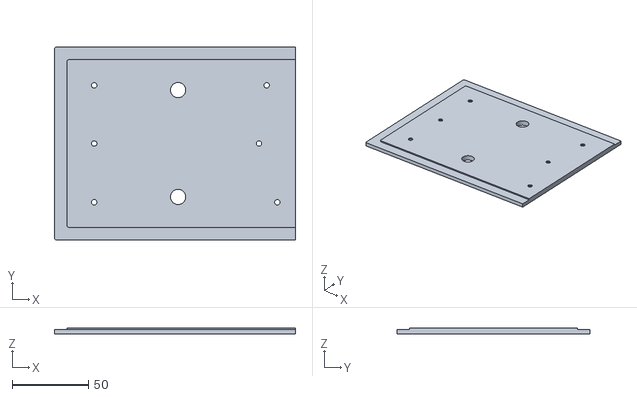
[picture p192: CAD file, 2022-11-19]
stl/andimoto7583/andimoto7584-frame-proMicro/andimoto7584-lidLeft-frame-proMicro.stl
157.9 x 126.3 x 4.00
