andimoto/keebcu/stl/andimotoSmallTKLiso/andimotoSmallTKLiso_keyboardRiser.stl

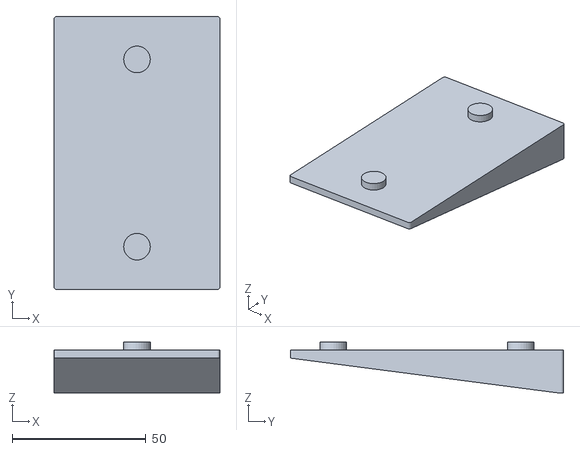
[picture p193: CAD file, 2022-10-18]
stl/andimotoSmallTKLiso/andimotoSmallTKLiso_keyboardRiser.stl
62.0 x 102.0 x 19.0
