andimoto/keebcu/stl/andimotoSmallTKLiso/andimotoSmallTKLiso_ALL-Lid-ProMicro.stl

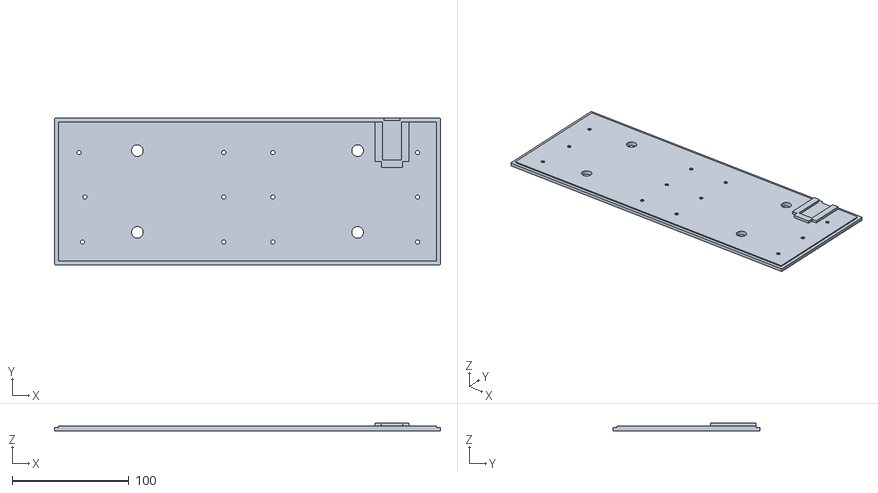
[picture p194: CAD file, 2022-10-18]
stl/andimotoSmallTKLiso/andimotoSmallTKLiso_ALL-Lid-ProMicro.stl
330.6 x 125.8 x 6.50
