andimoto/keebcu/wiring_sheets/andimmoto-numpad/andimoto-numpad-mirrored.png

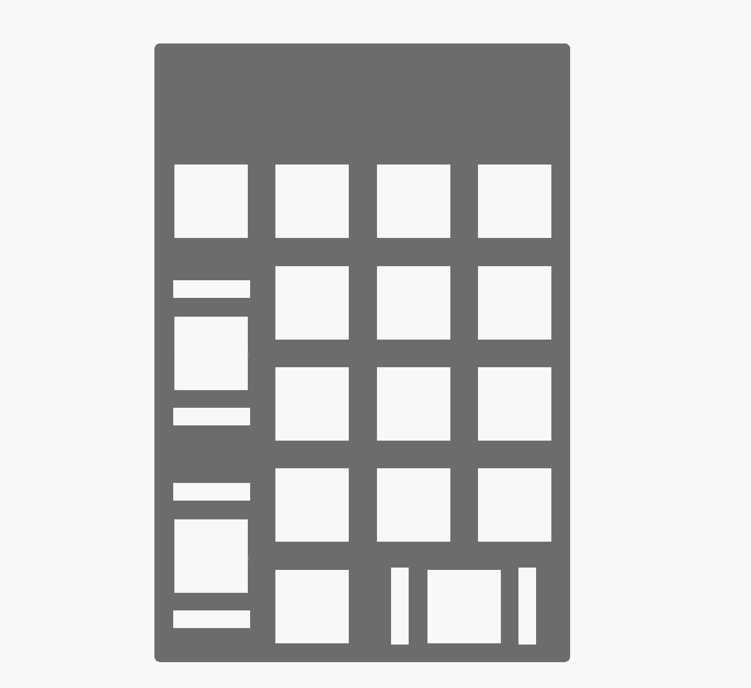
wiring_sheets/andimmoto-numpad/andimoto-numpad-mirrored.png
