andimoto/keebcu/wiring_sheets/andimmoto-numpad/andimoto-numpad.png

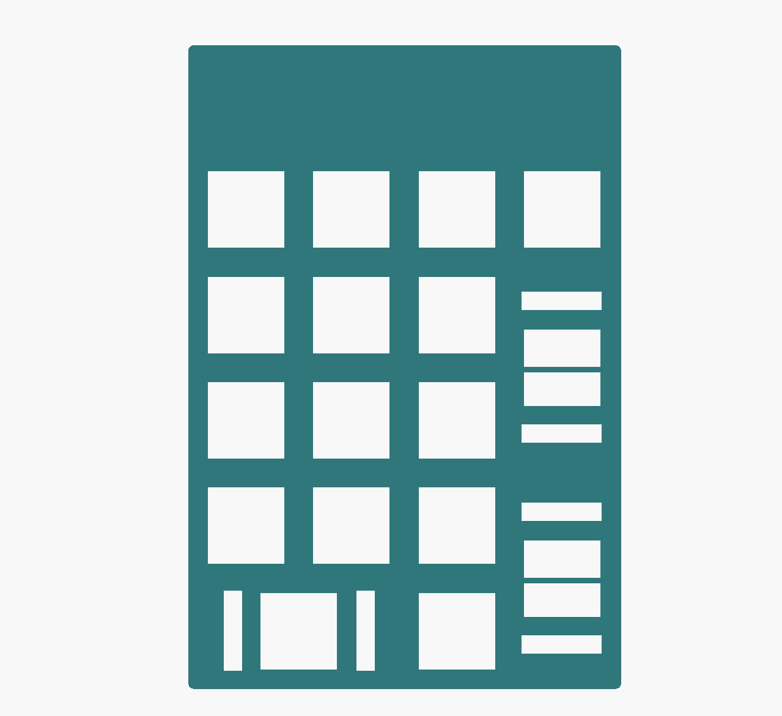
wiring_sheets/andimmoto-numpad/andimoto-numpad.png
