andimoto/keebcu/wiring_sheets/andimoto6064/andimoto6064.png

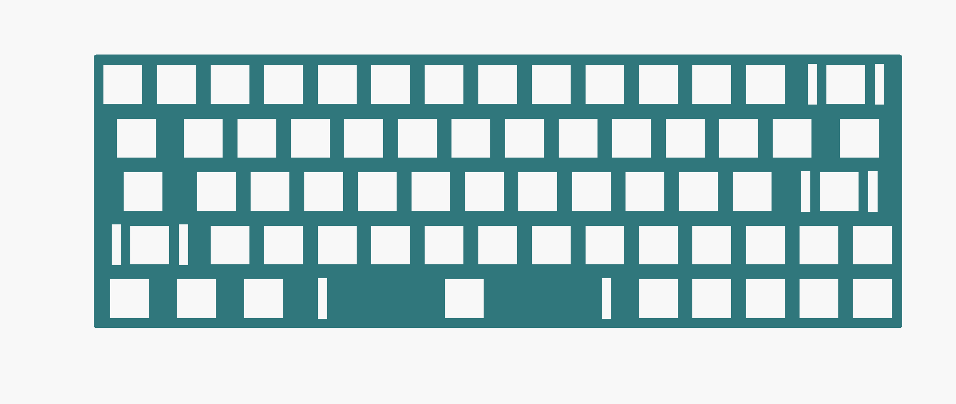
wiring_sheets/andimoto6064/andimoto6064.png
