andimoto/keebcu/wiring_sheets/andimoto7583/andimoto7583.png

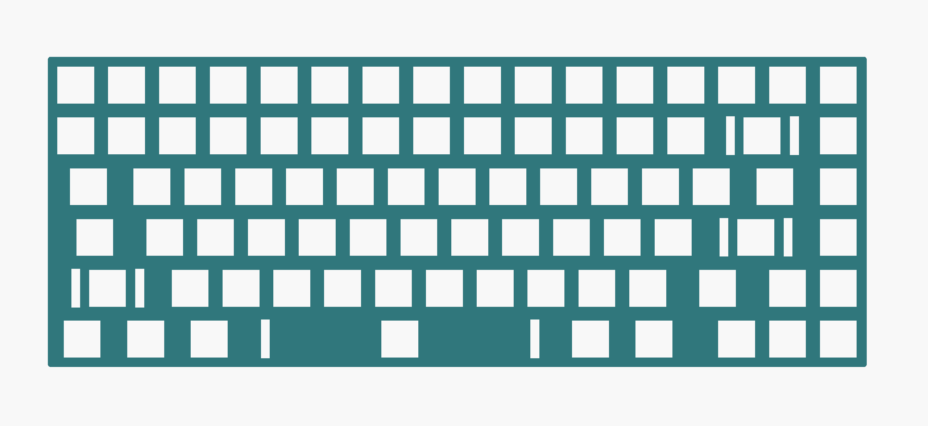
wiring_sheets/andimoto7583/andimoto7583.png
