andimoto/keebcu/wiring_sheets/andimoto_SmallTKL_iso/andimoto_smallTKL_iso.png

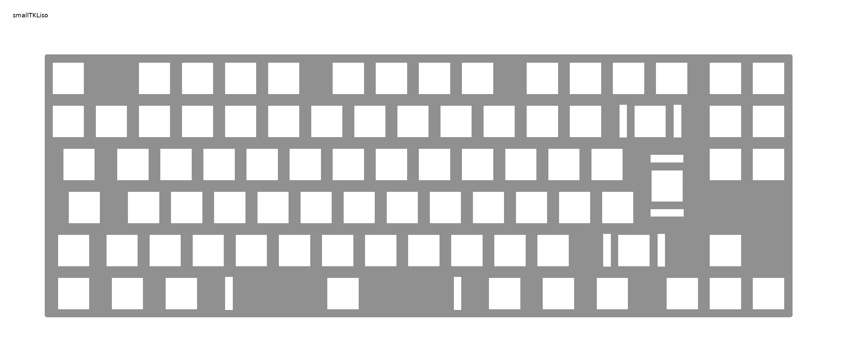
wiring_sheets/andimoto_SmallTKL_iso/andimoto_smallTKL_iso.png
