andimoto/keebcu/wiring_sheets/andimoto_SmallTKL_iso/andimoto_smallTKL_iso_mirrored.png

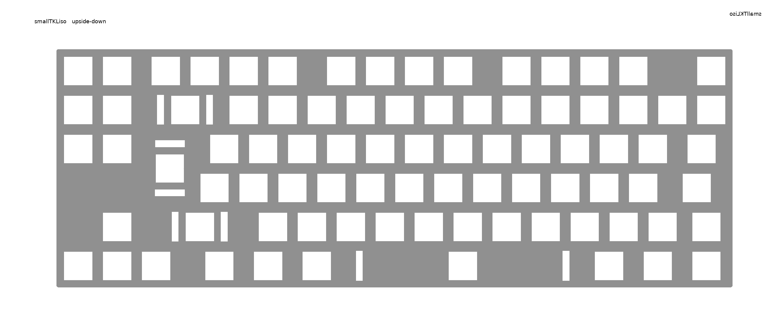
wiring_sheets/andimoto_SmallTKL_iso/andimoto_smallTKL_iso_mirrored.png
